A-N-Ulab/OTSI-cyberpet/graphics/otsi git baner/baner.png

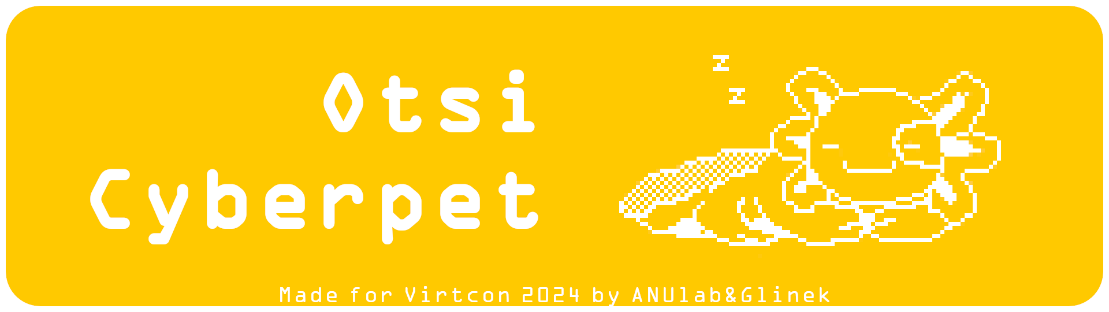
graphics/otsi git baner/baner.png
