A-N-Ulab/OTSI-cyberpet/graphics/renders and screenshots/render - back.png

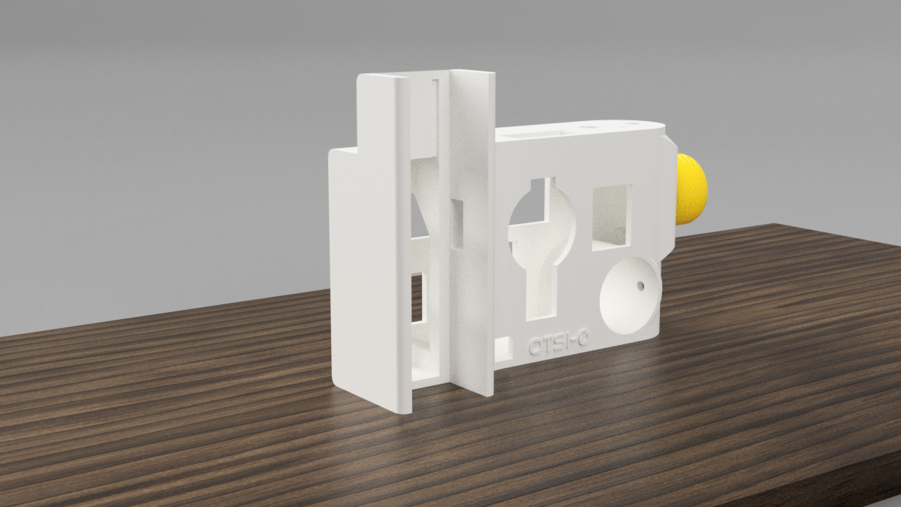
graphics/renders and screenshots/render - back.png
