A-N-Ulab/OTSI-cyberpet/graphics/renders and screenshots/render - front.png

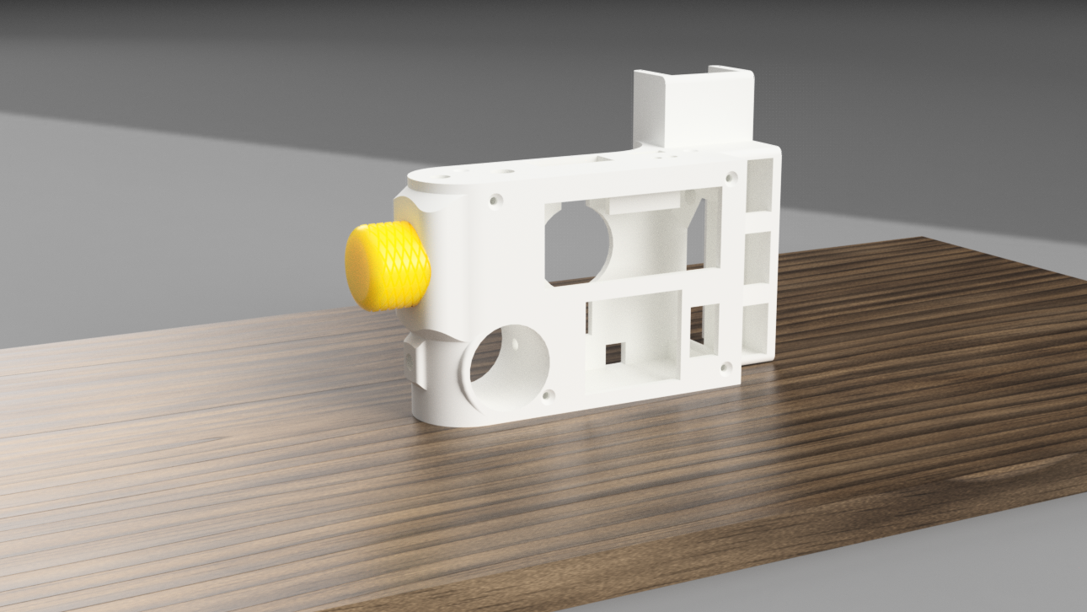
graphics/renders and screenshots/render - front.png
