A-N-Ulab/OTSI-cyberpet/graphics/renders and screenshots/render.jpg

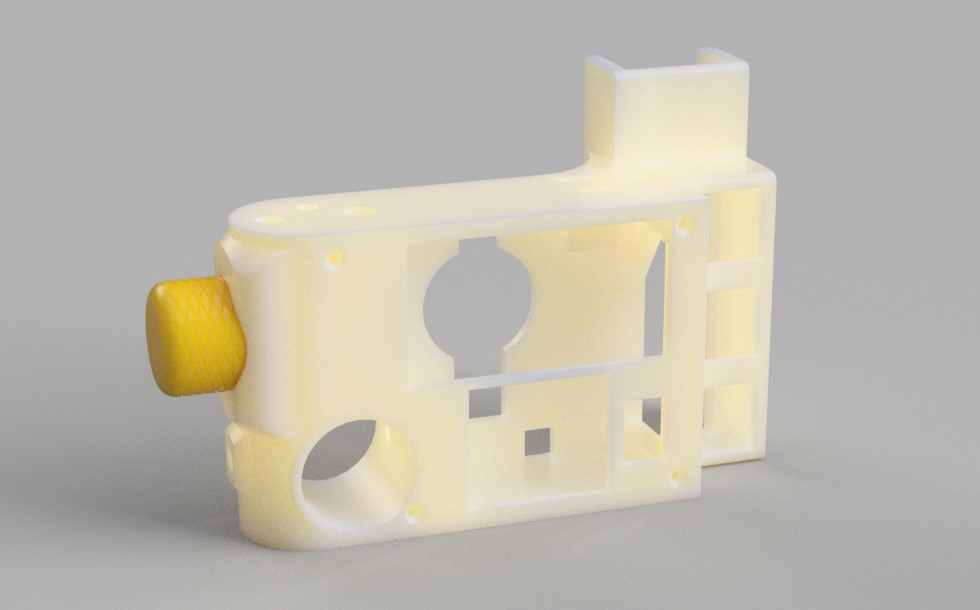
graphics/renders and screenshots/render.jpg
