A-N-Ulab/OTSI-cyberpet/graphics/renders and screenshots/Screenshot 2024-01-13 201948.jpg

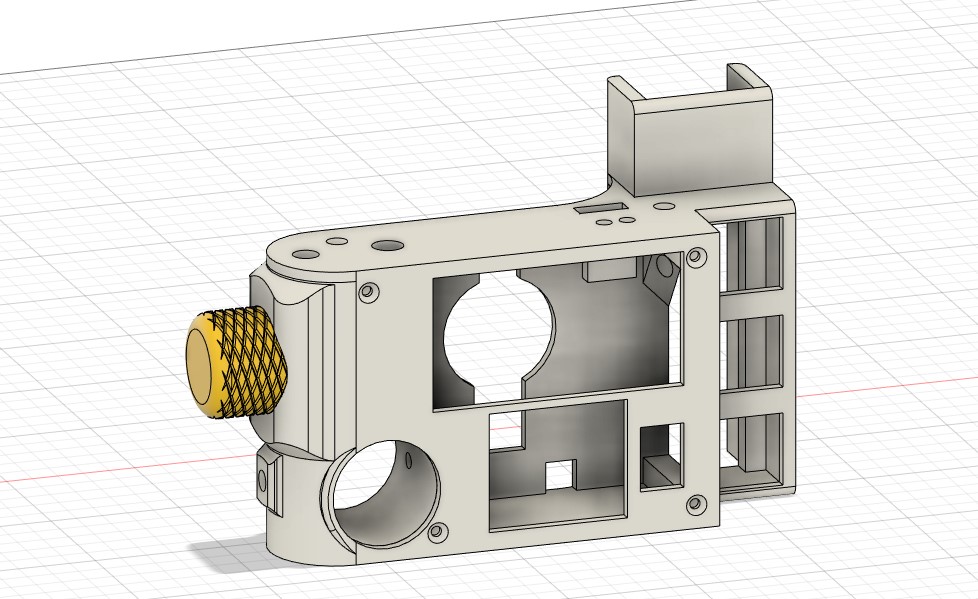
graphics/renders and screenshots/Screenshot 2024-01-13 201948.jpg
