A-N-Ulab/OTSI-cyberpet/Notes & Docs/Zrzut ekranu 2023-11-07 192916.jpg

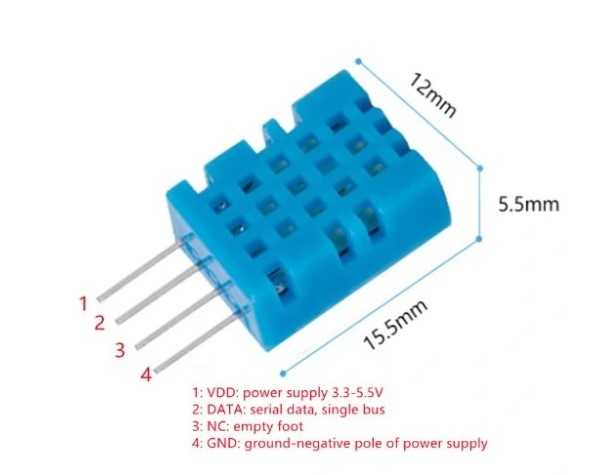
Notes & Docs/Zrzut ekranu 2023-11-07 192916.jpg
