A-N-Ulab/OTSI-cyberpet/photos/0a2272f7-c197-462a-a5be-fafe997e14a6.jpg

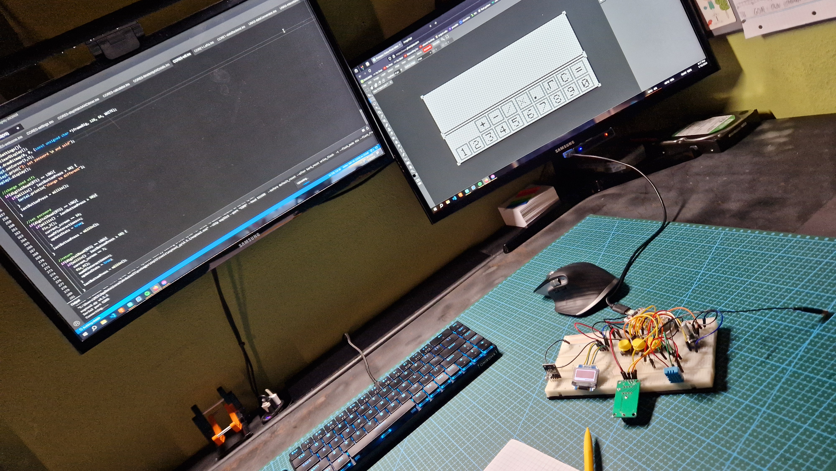
photos/0a2272f7-c197-462a-a5be-fafe997e14a6.jpg
