A-N-Ulab/OTSI-cyberpet/photos/20230913_195305.jpg

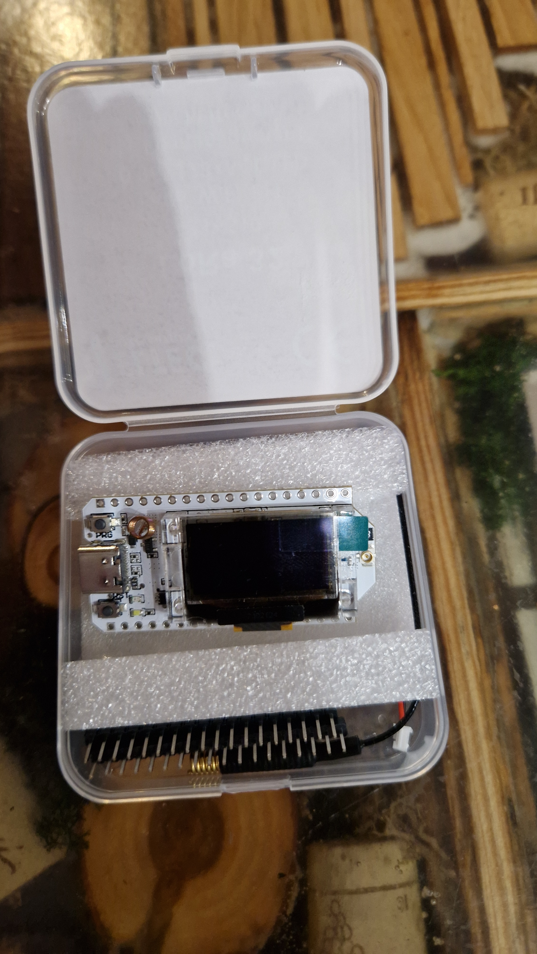
photos/20230913_195305.jpg
