A-N-Ulab/OTSI-cyberpet/photos/20230927_160514.jpg

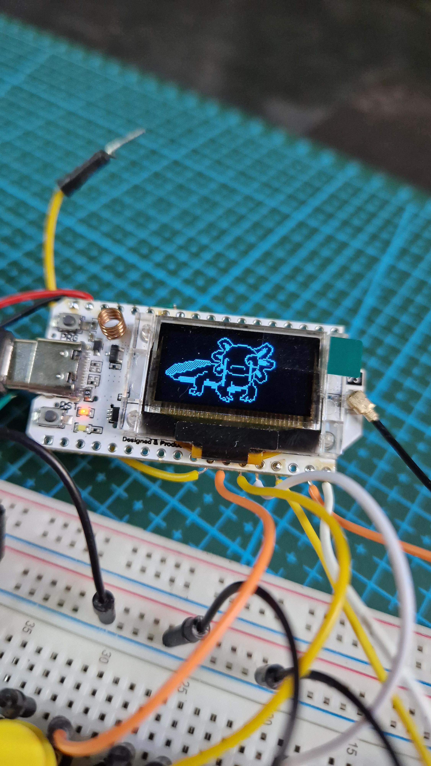
photos/20230927_160514.jpg
