A-N-Ulab/OTSI-cyberpet/photos/20230928_201221.jpg

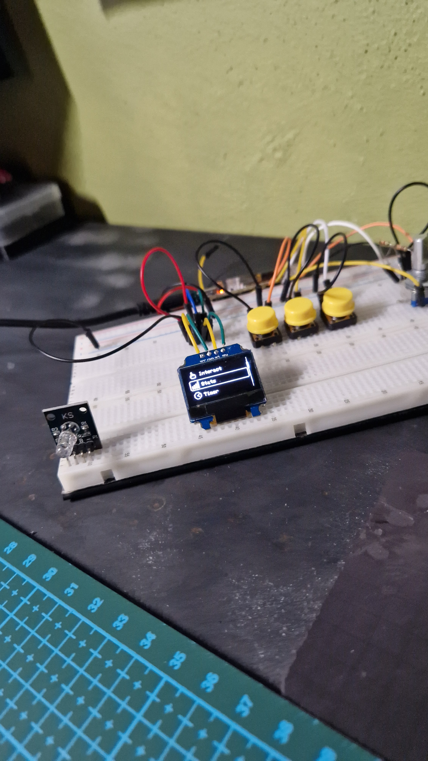
photos/20230928_201221.jpg
