A-N-Ulab/OTSI-cyberpet/photos/20231023_172651.jpg

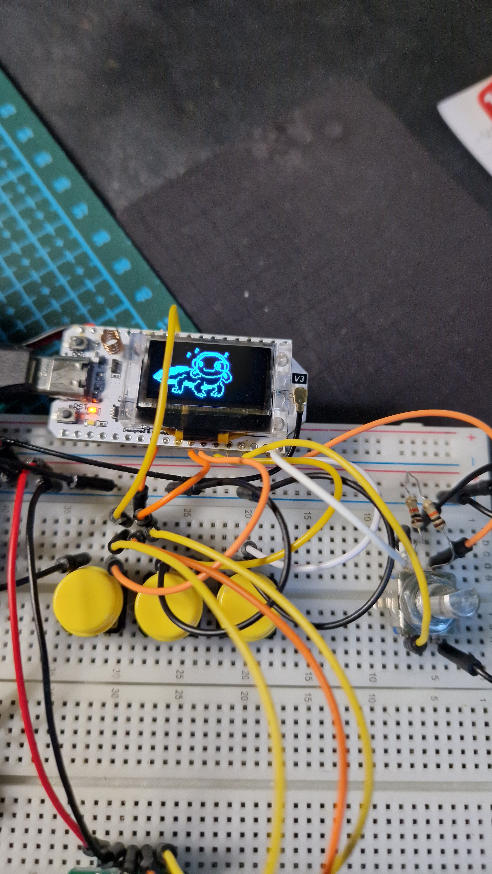
photos/20231023_172651.jpg
