A-N-Ulab/OTSI-cyberpet/photos/20240121_212100.jpg

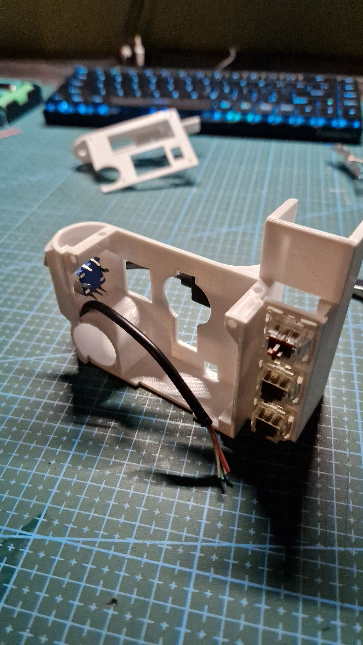
photos/20240121_212100.jpg
