A-N-Ulab/OTSI-cyberpet/photos/20240121_212102.jpg

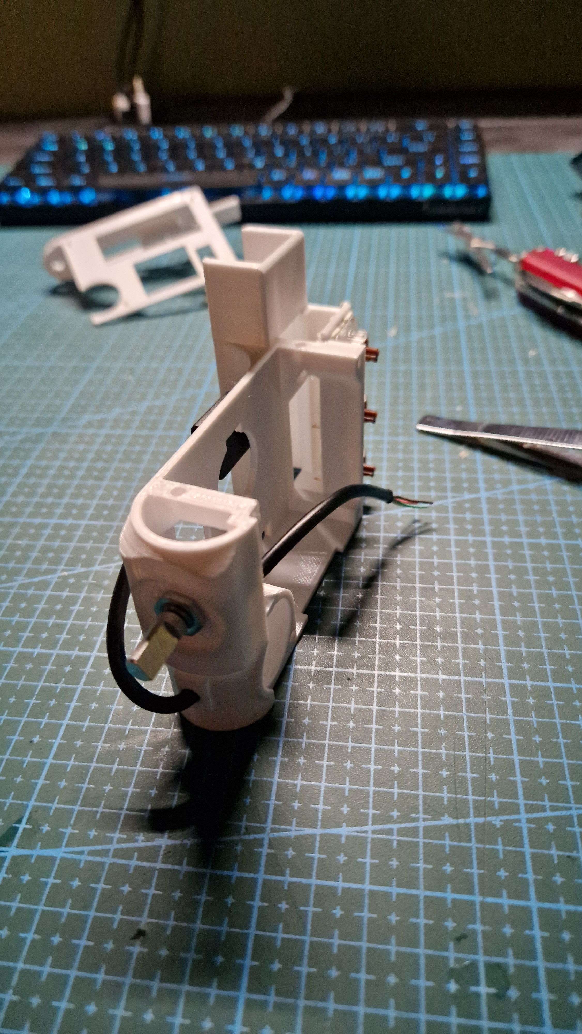
photos/20240121_212102.jpg
