A-N-Ulab/OTSI-cyberpet/photos/20240121_212109.jpg

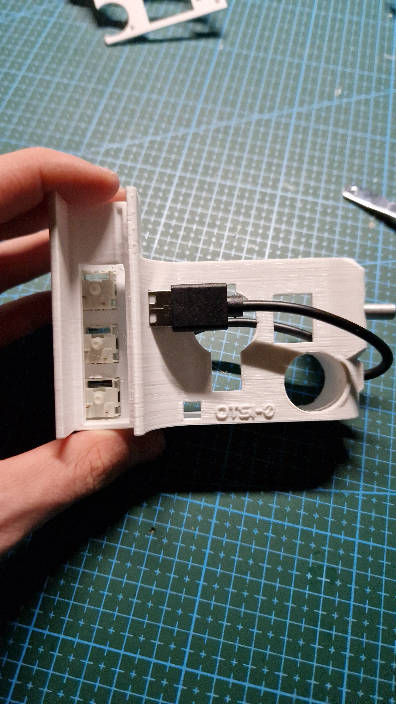
photos/20240121_212109.jpg
