A-N-Ulab/OTSI-cyberpet/photos/20240122_054914.jpg

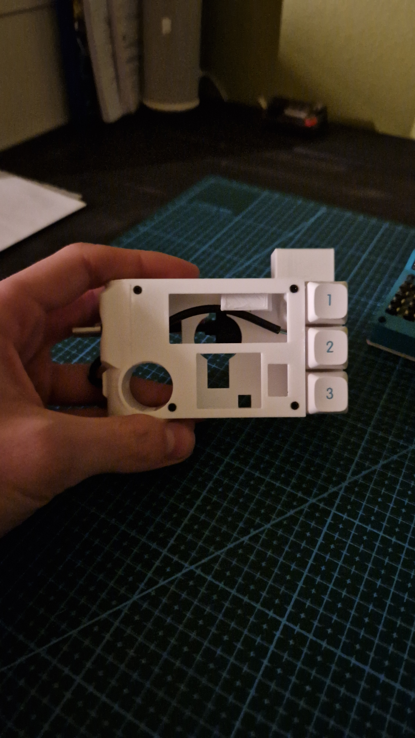
photos/20240122_054914.jpg
