A-N-Ulab/OTSI-cyberpet/photos/20240122_203220.jpg

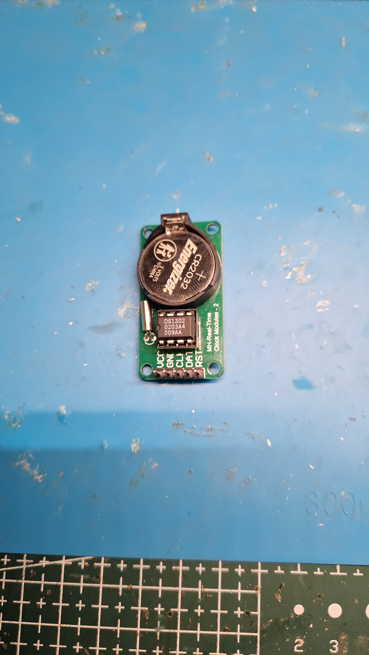
photos/20240122_203220.jpg
