A-N-Ulab/OTSI-cyberpet/photos/20240122_203737.jpg

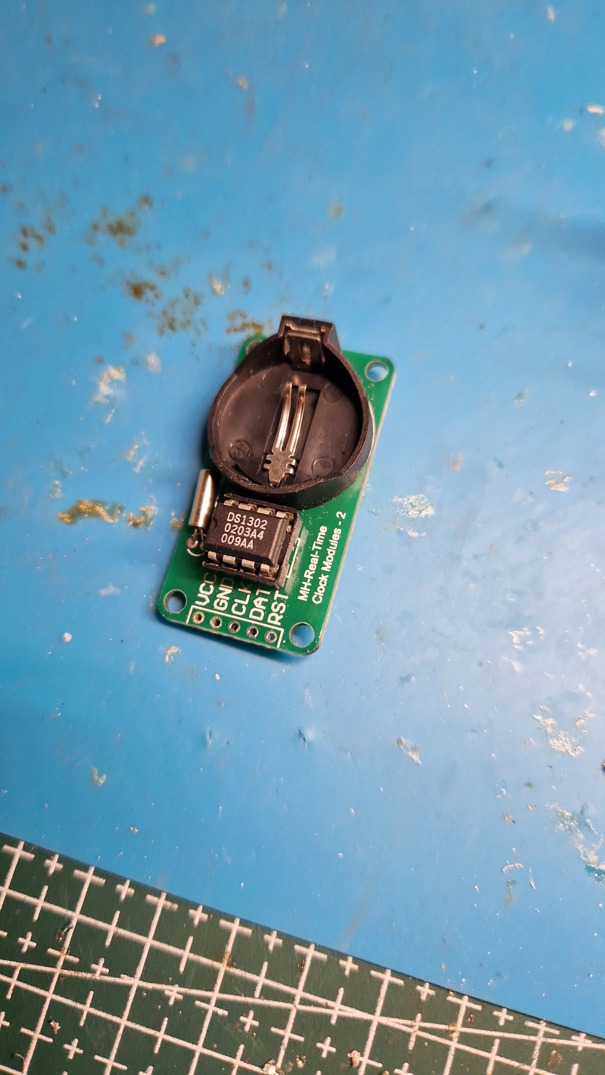
photos/20240122_203737.jpg
