A-N-Ulab/OTSI-cyberpet/photos/20240122_203856.jpg

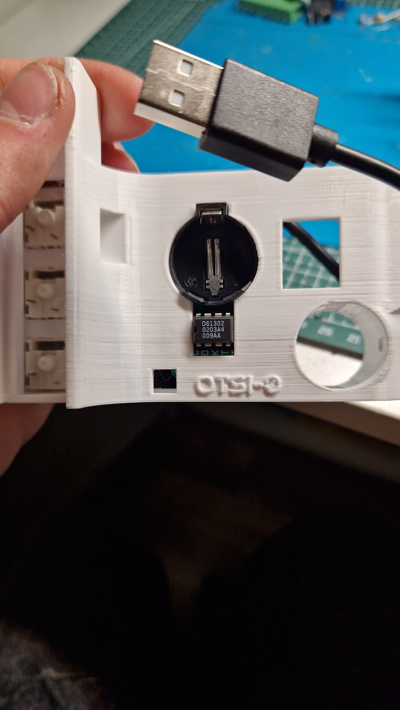
photos/20240122_203856.jpg
