A-N-Ulab/OTSI-cyberpet/photos/20240122_203859.jpg

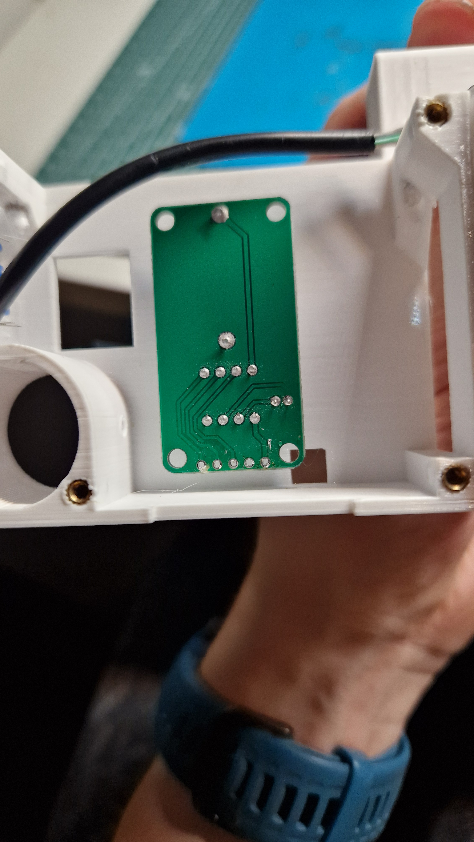
photos/20240122_203859.jpg
