A-N-Ulab/OTSI-cyberpet/photos/20240122_203900.jpg

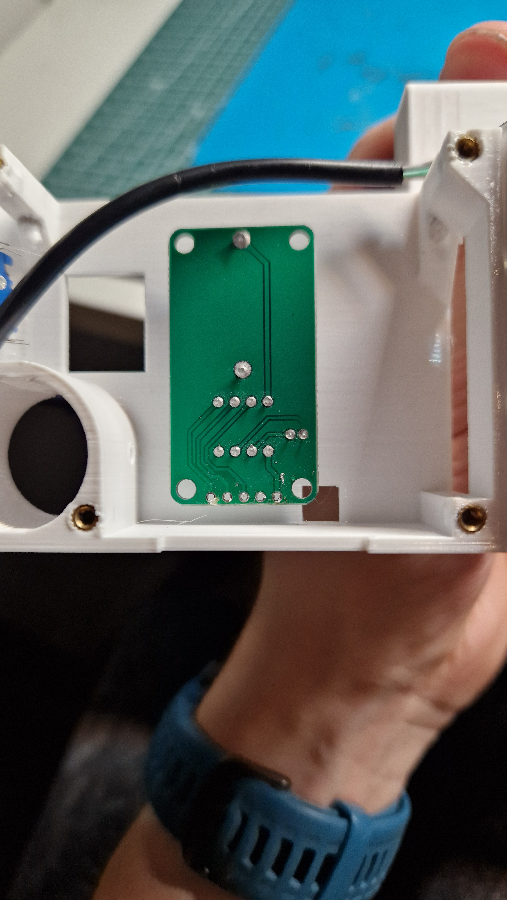
photos/20240122_203900.jpg
