A-N-Ulab/OTSI-cyberpet/photos/20240122_204321.jpg

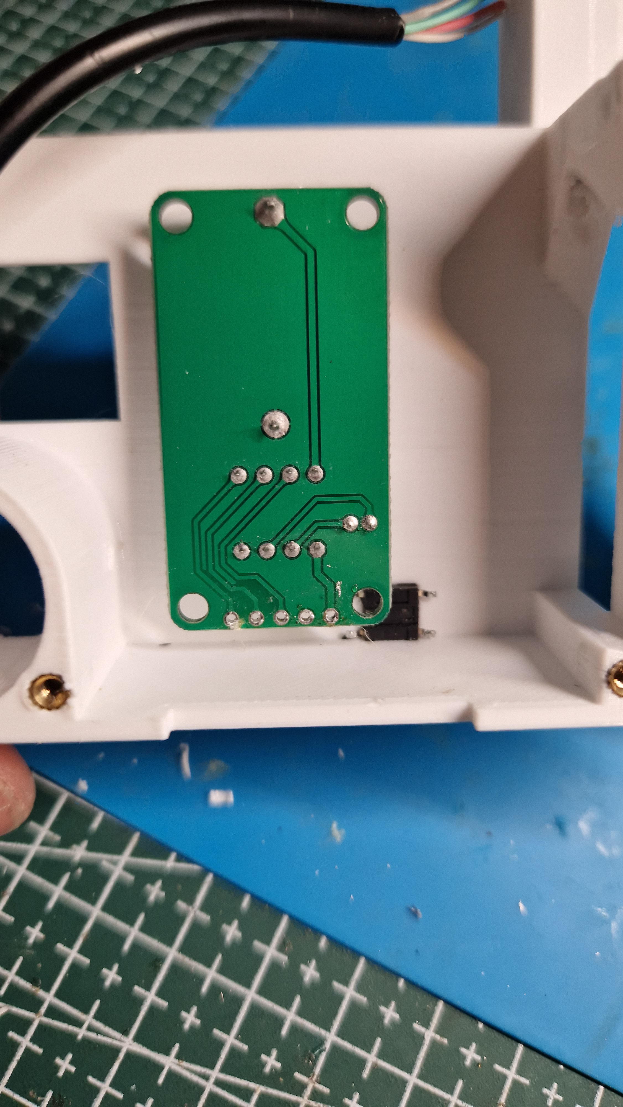
photos/20240122_204321.jpg
