A-N-Ulab/OTSI-cyberpet/photos/20240122_204324.jpg

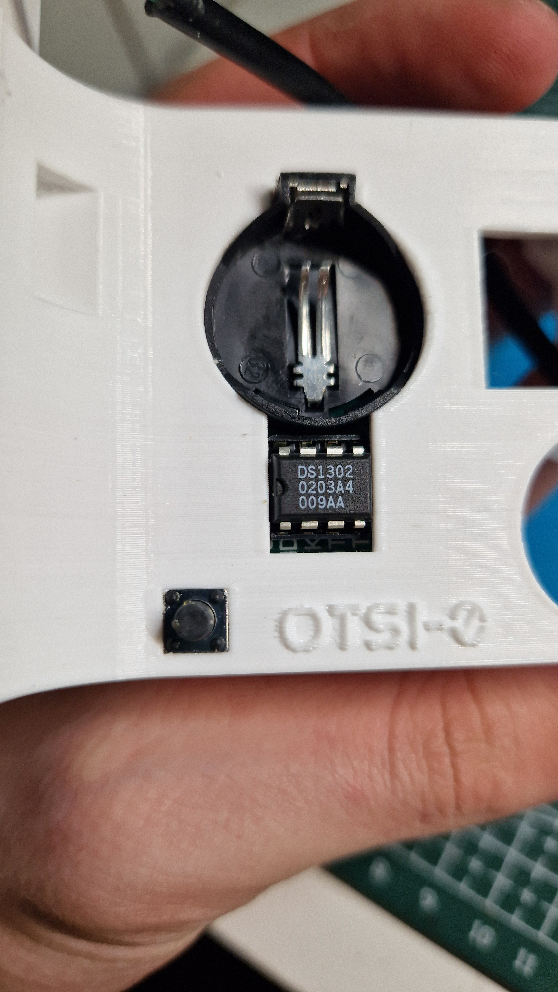
photos/20240122_204324.jpg
