A-N-Ulab/OTSI-cyberpet/photos/20240122_205355.jpg

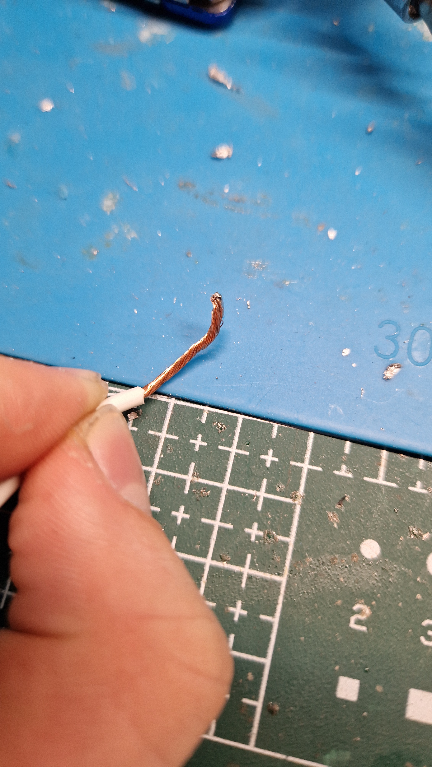
photos/20240122_205355.jpg
