A-N-Ulab/OTSI-cyberpet/photos/20240122_205412.jpg

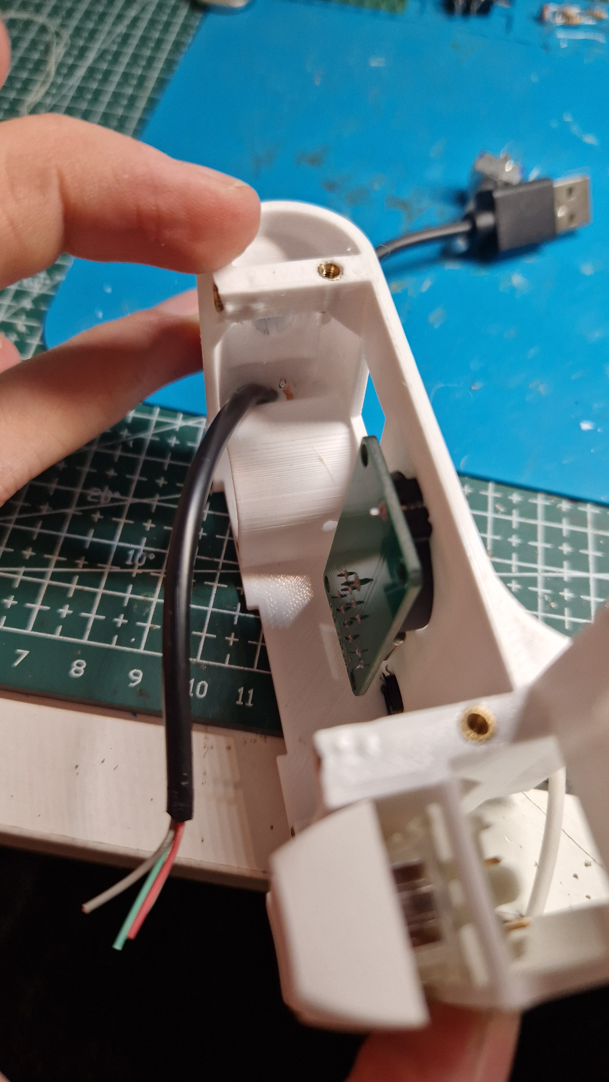
photos/20240122_205412.jpg
