A-N-Ulab/OTSI-cyberpet/photos/20240122_205949.jpg

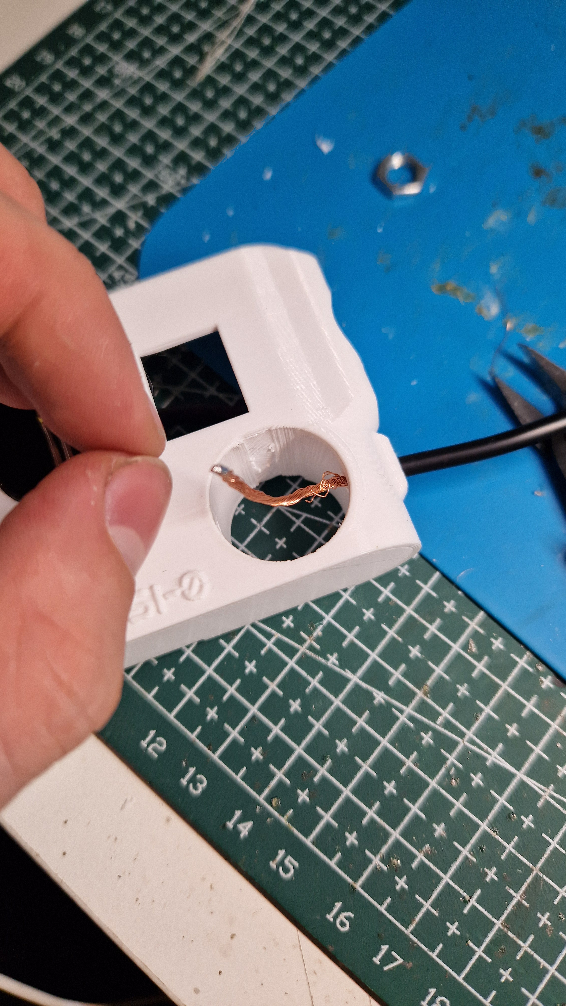
photos/20240122_205949.jpg
