A-N-Ulab/OTSI-cyberpet/photos/20240122_205954.jpg

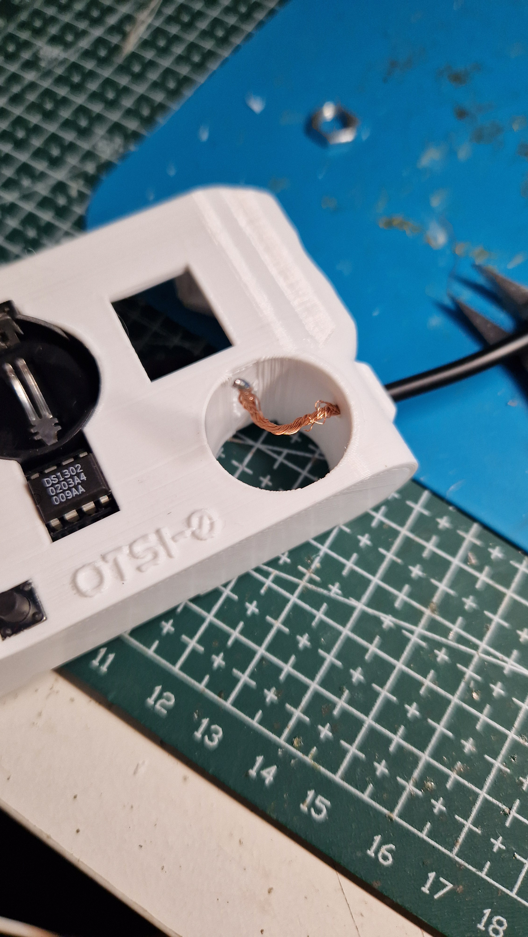
photos/20240122_205954.jpg
