A-N-Ulab/OTSI-cyberpet/photos/20240122_210243.jpg

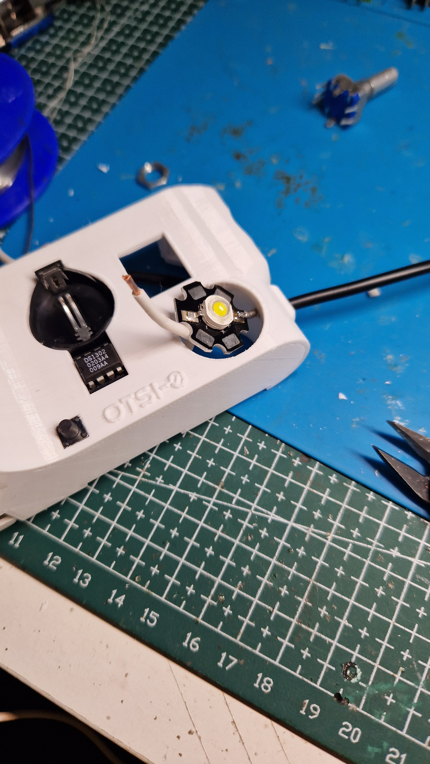
photos/20240122_210243.jpg
