A-N-Ulab/OTSI-cyberpet/photos/20240122_210559.jpg

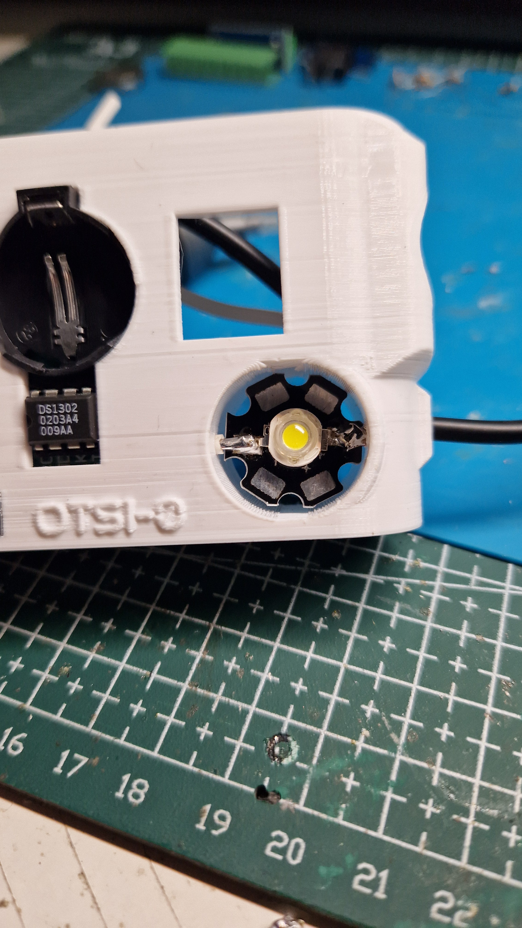
photos/20240122_210559.jpg
