A-N-Ulab/OTSI-cyberpet/photos/20240122_210723.jpg

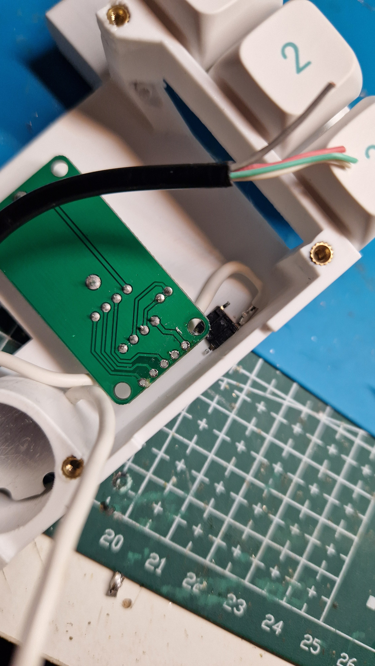
photos/20240122_210723.jpg
