A-N-Ulab/OTSI-cyberpet/photos/20240122_210949.jpg

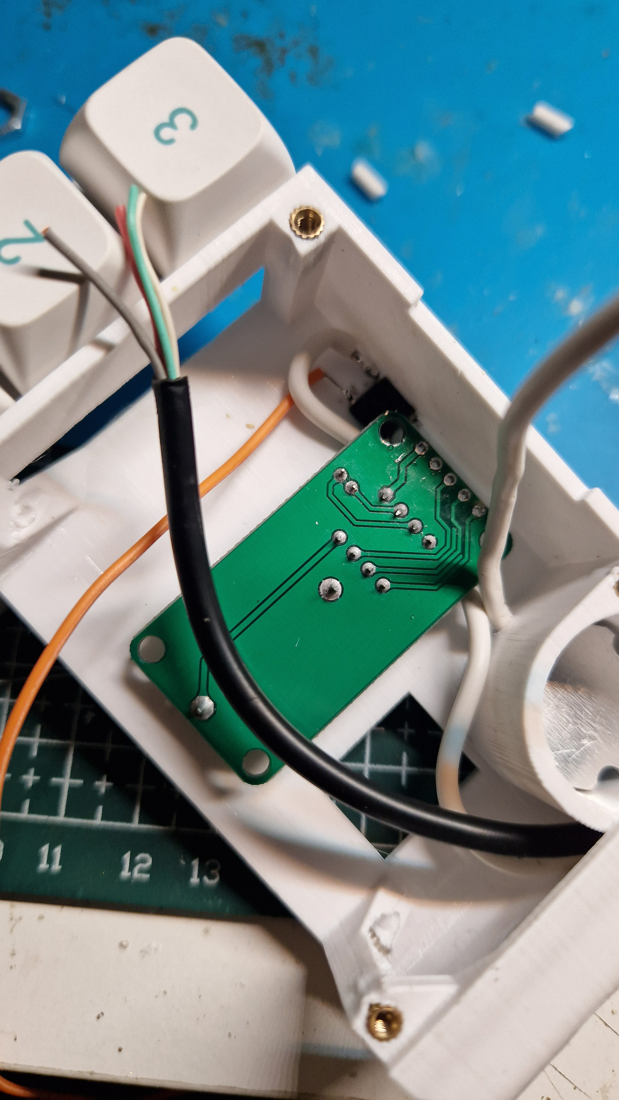
photos/20240122_210949.jpg
