A-N-Ulab/OTSI-cyberpet/photos/20240122_211322.jpg

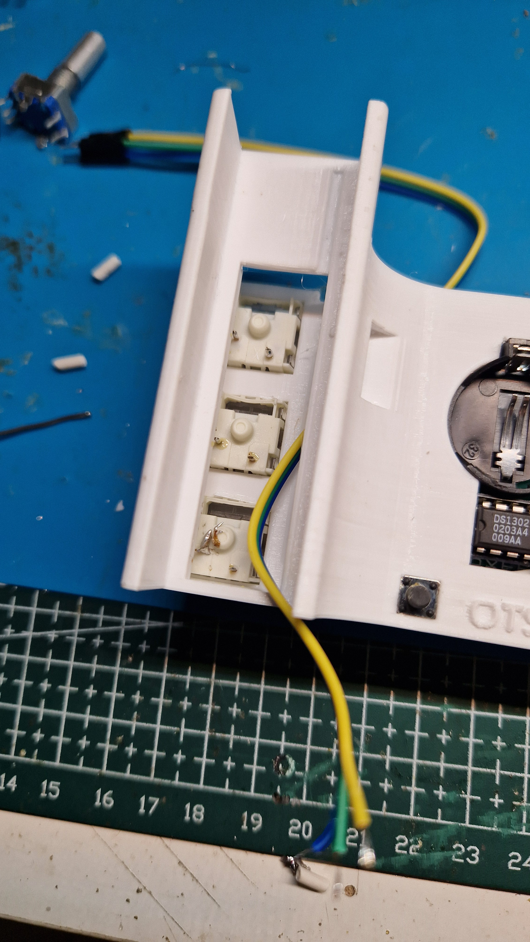
photos/20240122_211322.jpg
