A-N-Ulab/OTSI-cyberpet/photos/20240122_211459.jpg

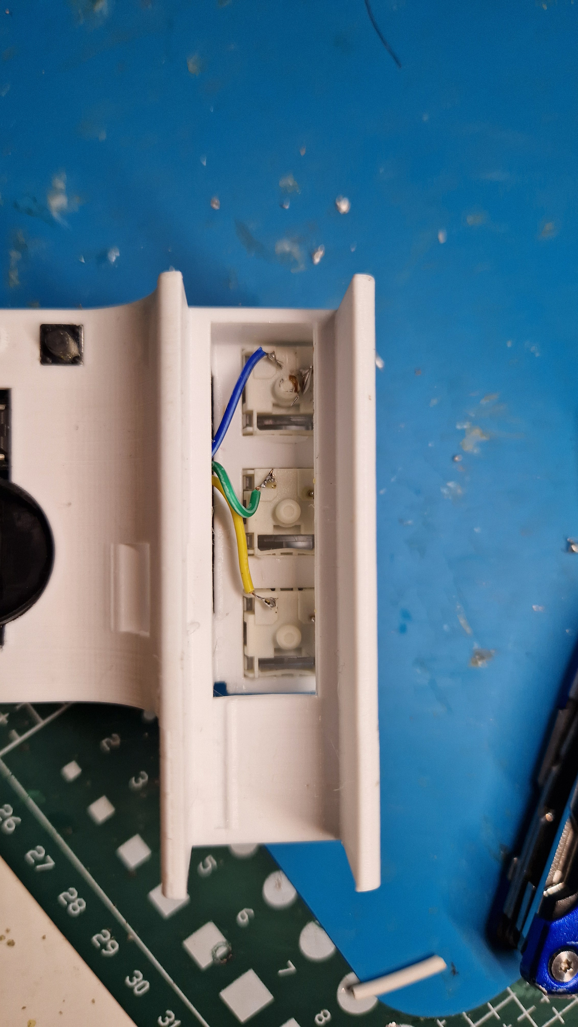
photos/20240122_211459.jpg
