A-N-Ulab/OTSI-cyberpet/photos/20240122_211742.jpg

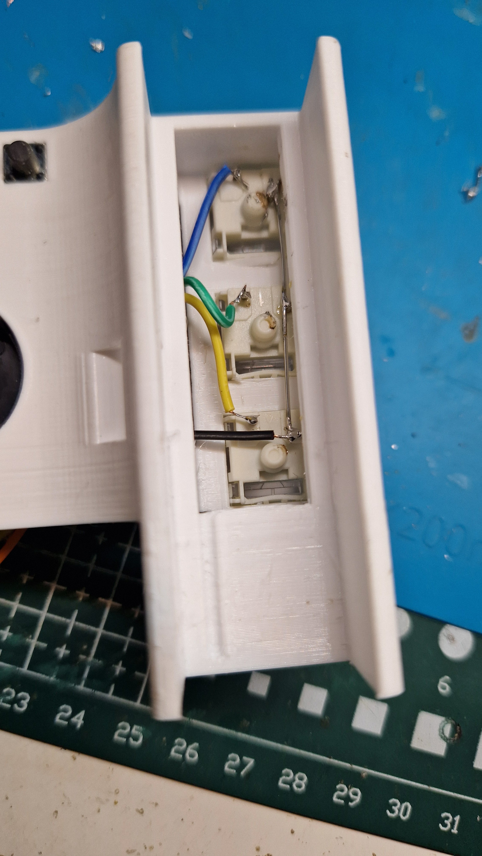
photos/20240122_211742.jpg
