A-N-Ulab/OTSI-cyberpet/photos/20240122_211933.jpg

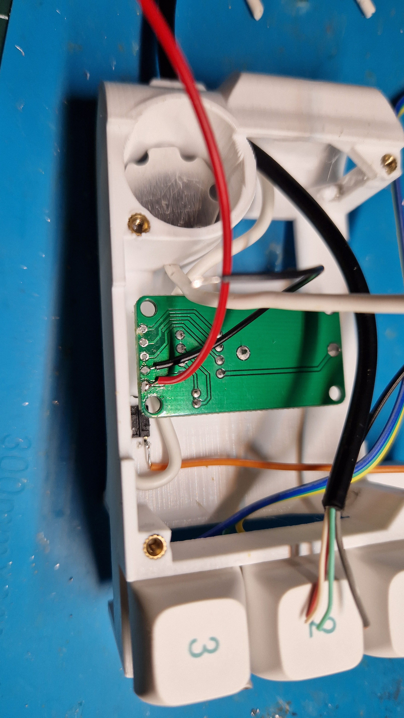
photos/20240122_211933.jpg
