A-N-Ulab/OTSI-cyberpet/photos/20240122_212038.jpg

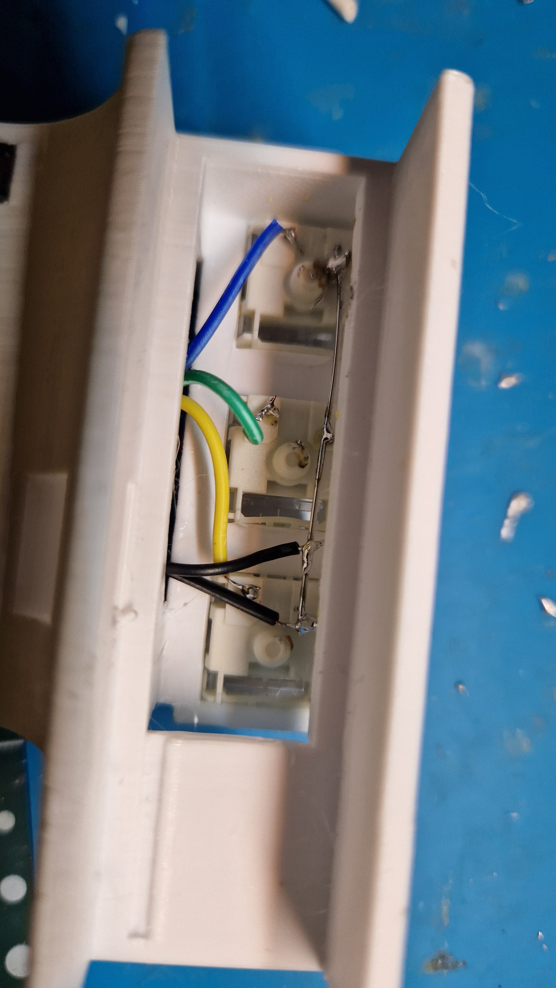
photos/20240122_212038.jpg
