A-N-Ulab/OTSI-cyberpet/photos/20240122_212201.jpg

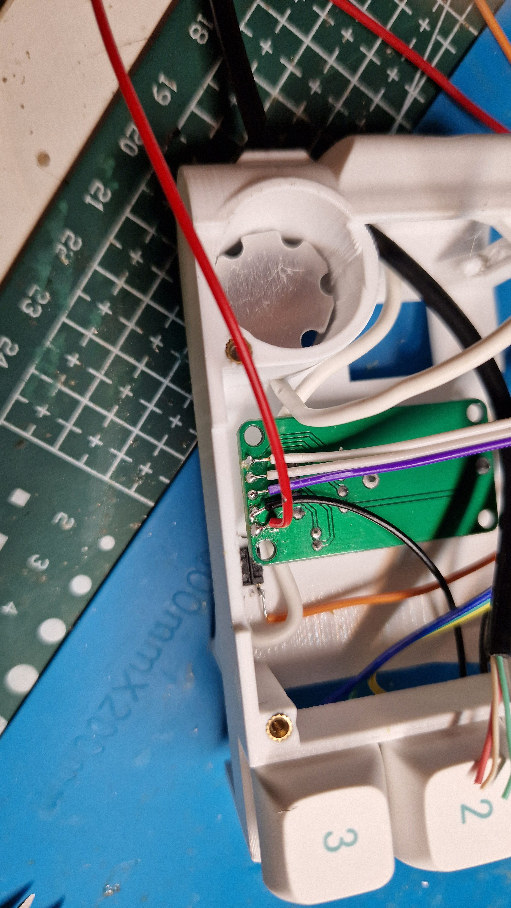
photos/20240122_212201.jpg
