A-N-Ulab/OTSI-cyberpet/photos/20240122_212416.jpg

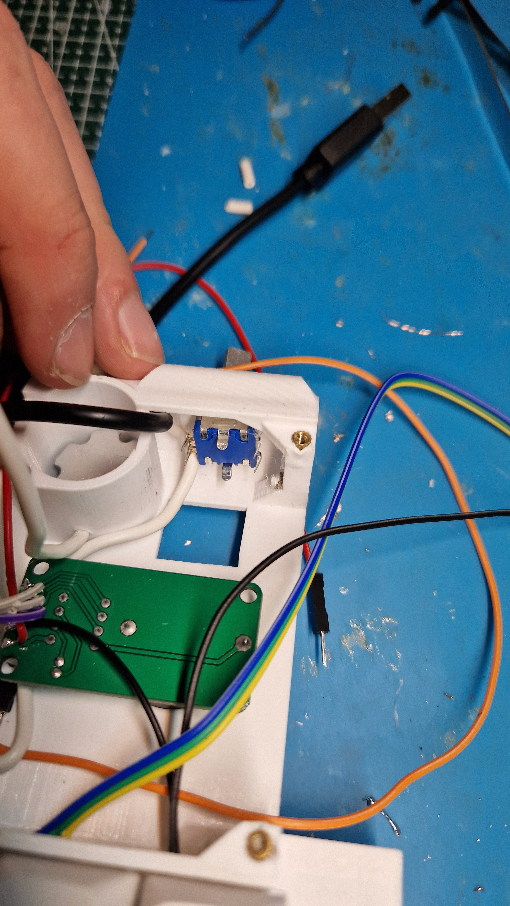
photos/20240122_212416.jpg
