A-N-Ulab/OTSI-cyberpet/photos/20240122_213624.jpg

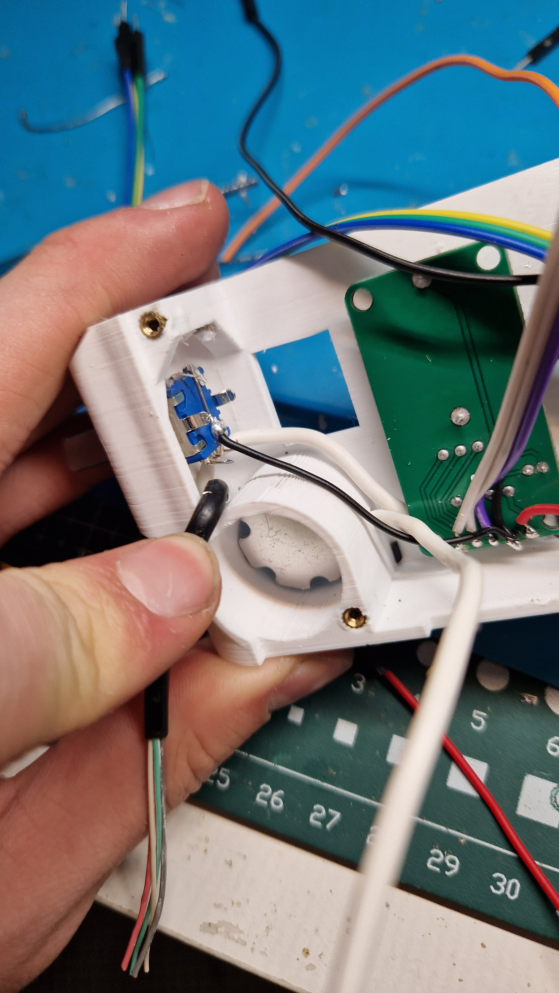
photos/20240122_213624.jpg
