A-N-Ulab/OTSI-cyberpet/photos/20240122_213839.jpg

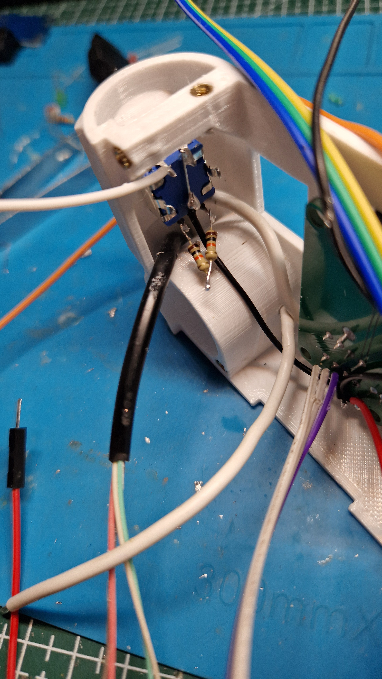
photos/20240122_213839.jpg
