A-N-Ulab/OTSI-cyberpet/photos/20240122_214125.jpg

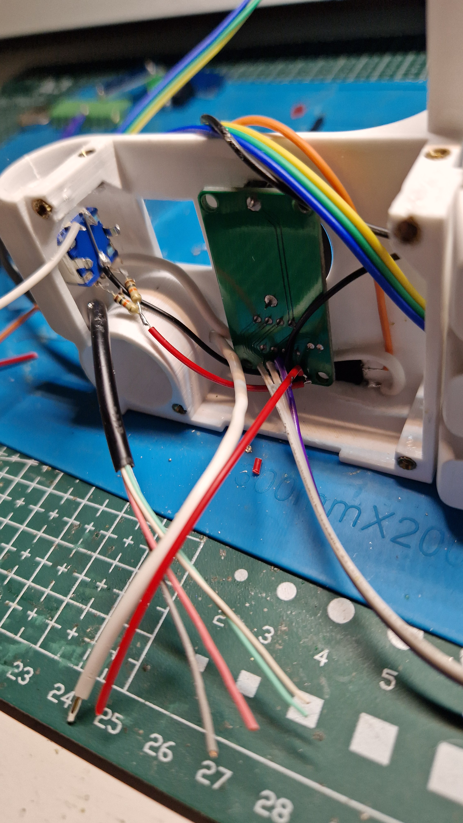
photos/20240122_214125.jpg
