A-N-Ulab/OTSI-cyberpet/photos/20240122_214958.jpg

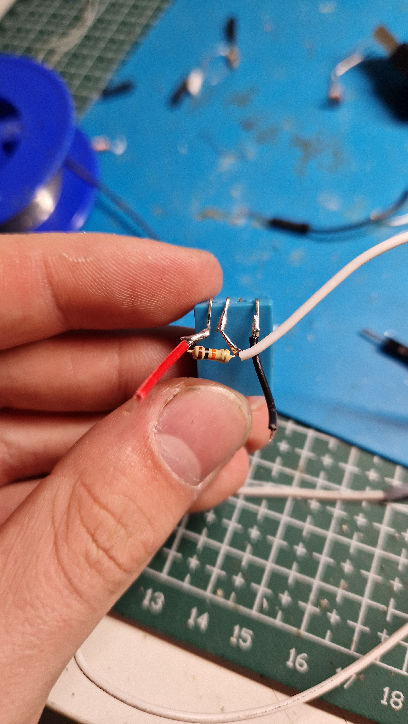
photos/20240122_214958.jpg
