A-N-Ulab/OTSI-cyberpet/photos/20240122_220841.jpg

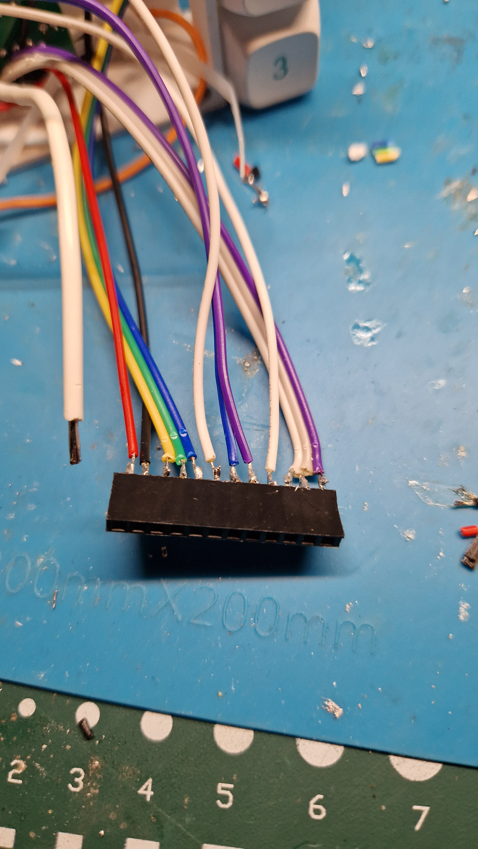
photos/20240122_220841.jpg
