A-N-Ulab/OTSI-cyberpet/photos/20240122_221745.jpg

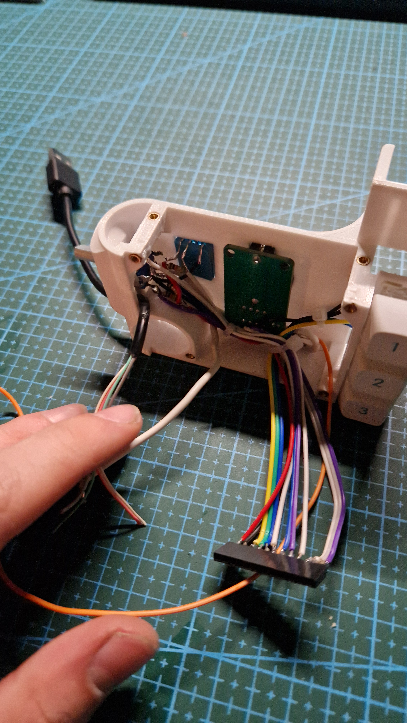
photos/20240122_221745.jpg
