A-N-Ulab/OTSI-cyberpet/photos/20240123_164509.jpg

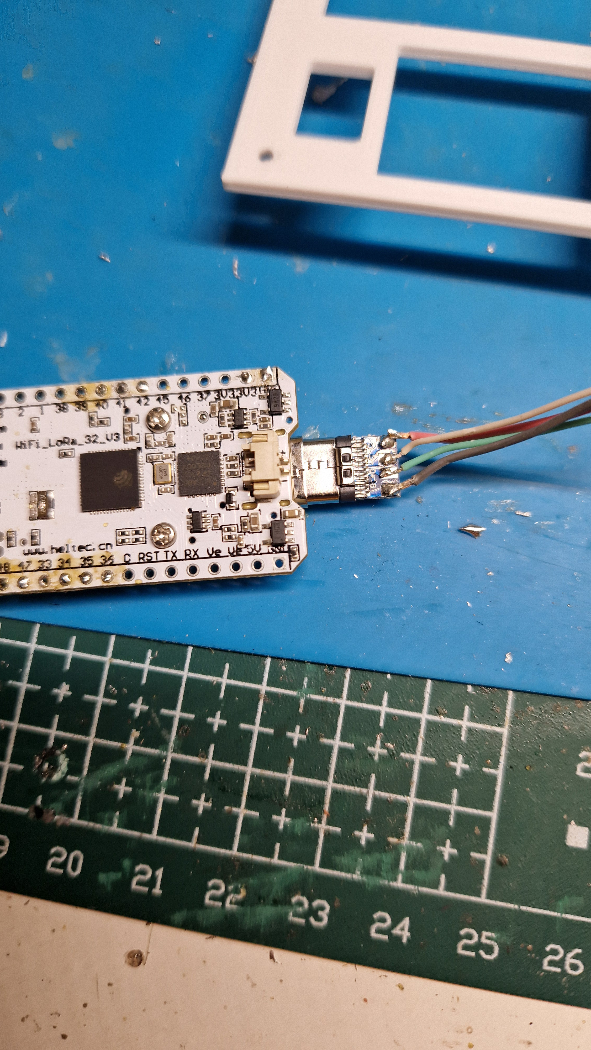
photos/20240123_164509.jpg
