A-N-Ulab/OTSI-cyberpet/photos/20240123_164611.jpg

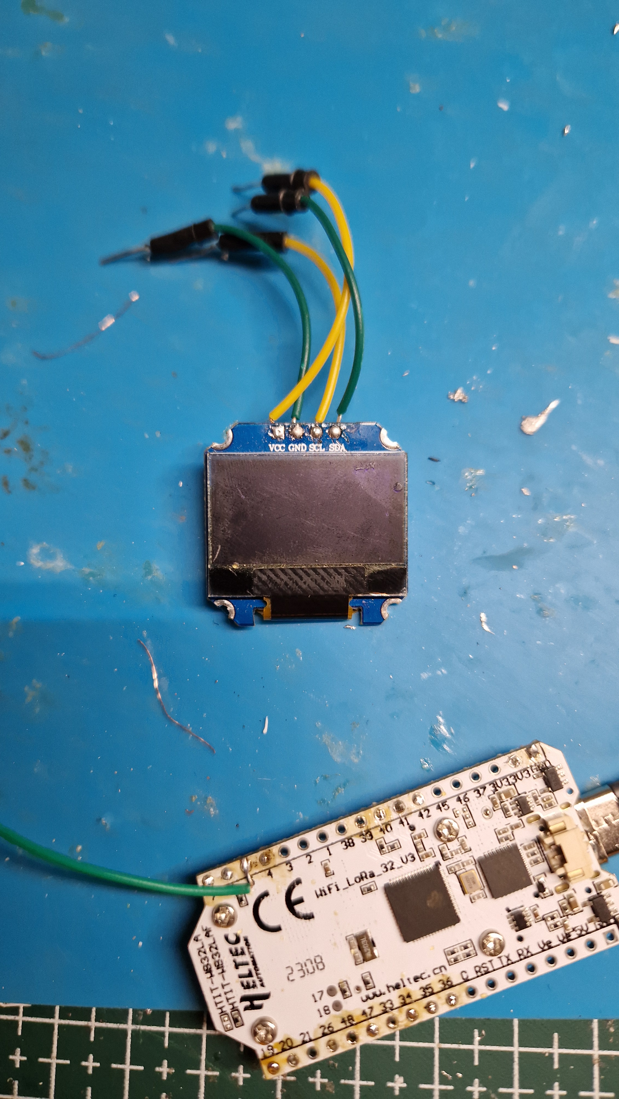
photos/20240123_164611.jpg
