A-N-Ulab/OTSI-cyberpet/photos/20240123_165450.jpg

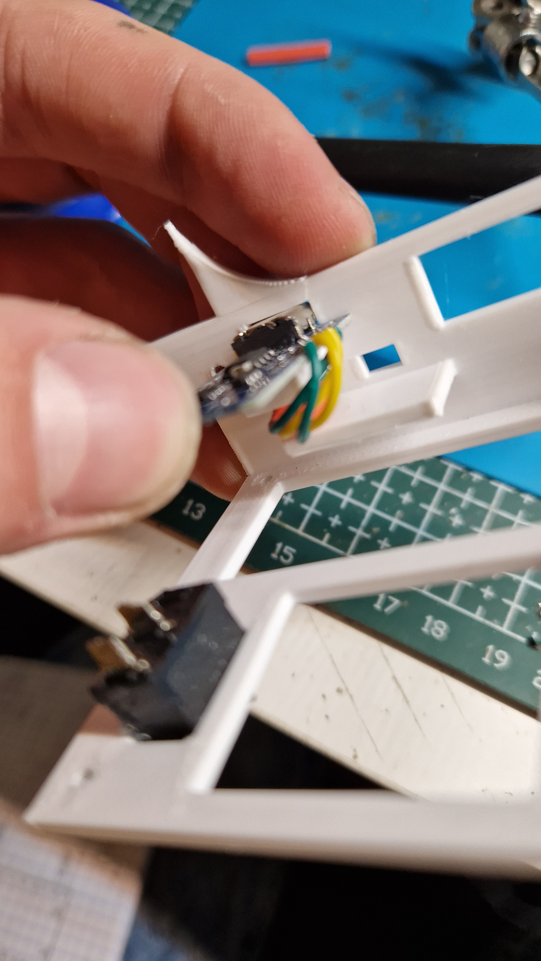
photos/20240123_165450.jpg
