A-N-Ulab/OTSI-cyberpet/photos/20240123_172744.jpg

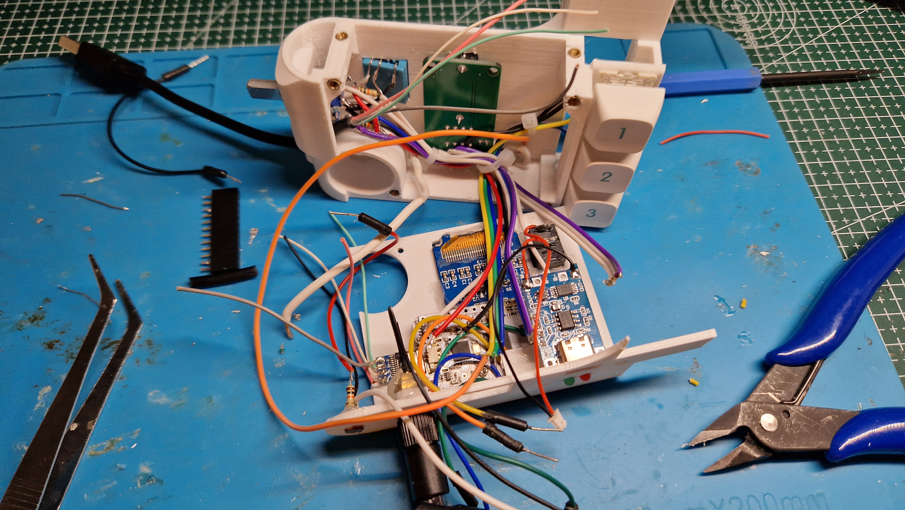
photos/20240123_172744.jpg
