A-N-Ulab/OTSI-cyberpet/photos/20240123_211852.jpg

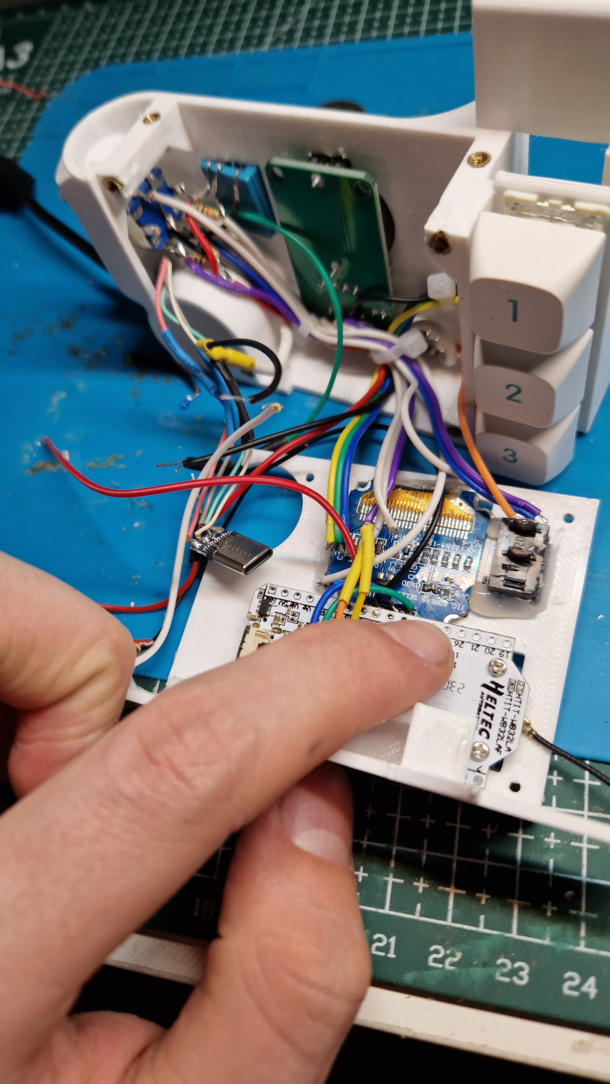
photos/20240123_211852.jpg
