A-N-Ulab/OTSI-cyberpet/photos/20240123_223442.jpg

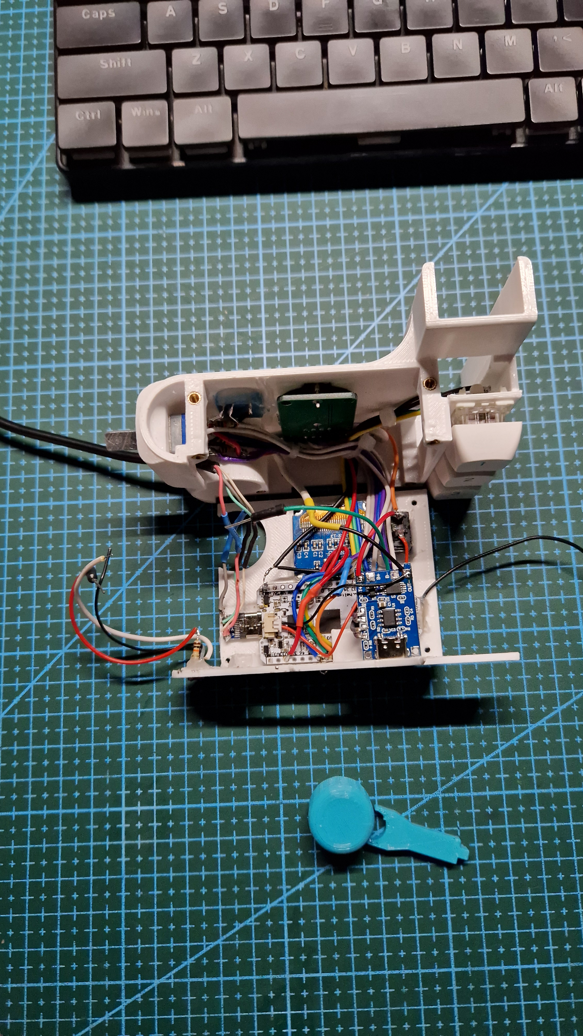
photos/20240123_223442.jpg
