A-N-Ulab/OTSI-cyberpet/photos/20240124_095504.jpg

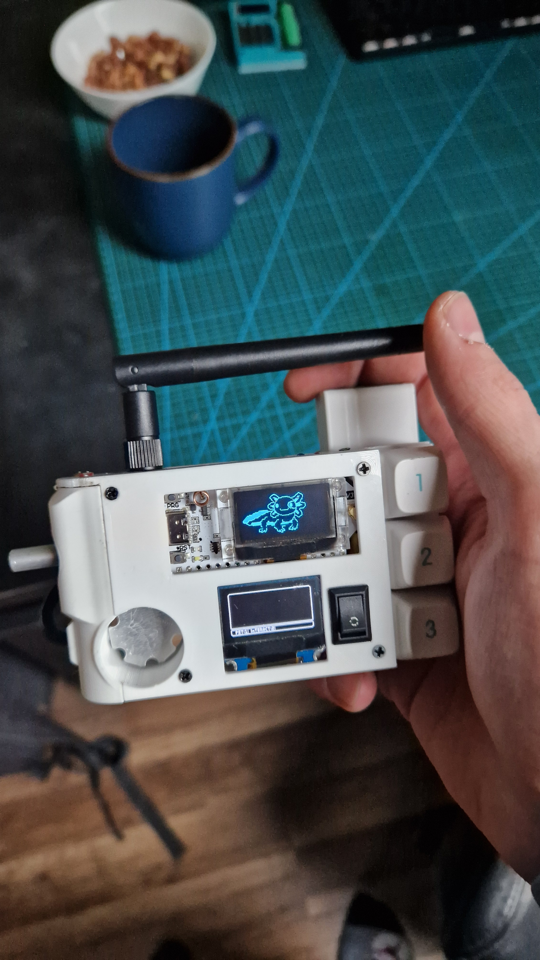
photos/20240124_095504.jpg
