A-N-Ulab/OTSI-cyberpet/photos/20240124_214952.jpg

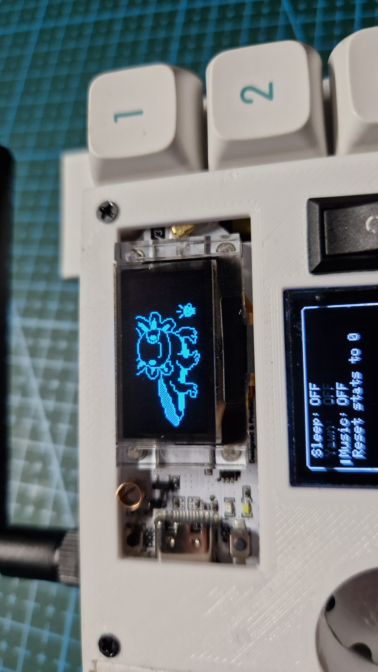
photos/20240124_214952.jpg
