A-N-Ulab/OTSI-cyberpet/photos/20240127_142506.jpg

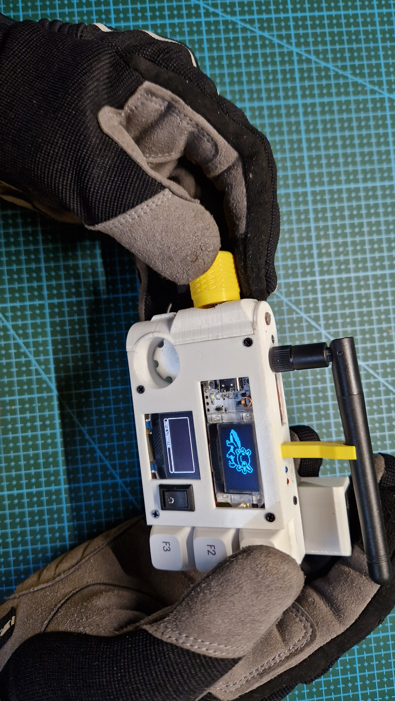
photos/20240127_142506.jpg
