A-N-Ulab/OTSI-cyberpet/photos/20240127_143146.jpg

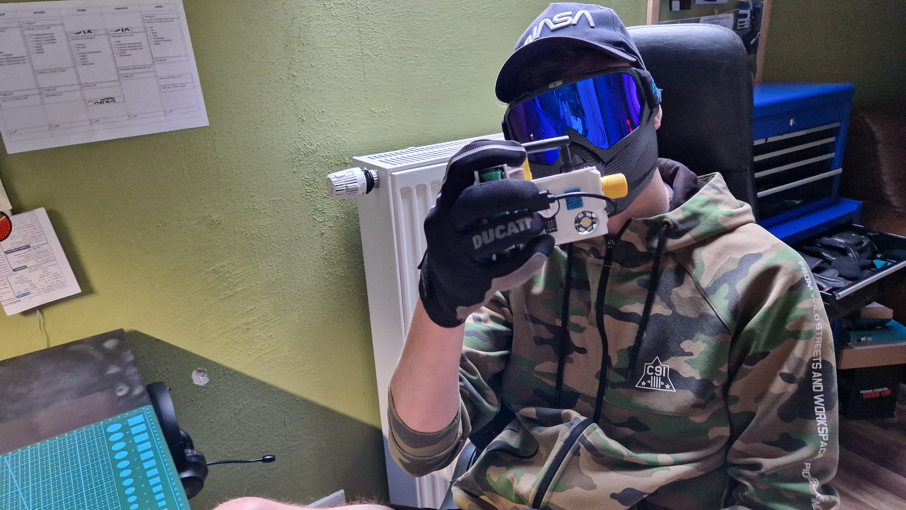
photos/20240127_143146.jpg
