A-N-Ulab/OTSI-cyberpet/photos/20240127_143203.jpg

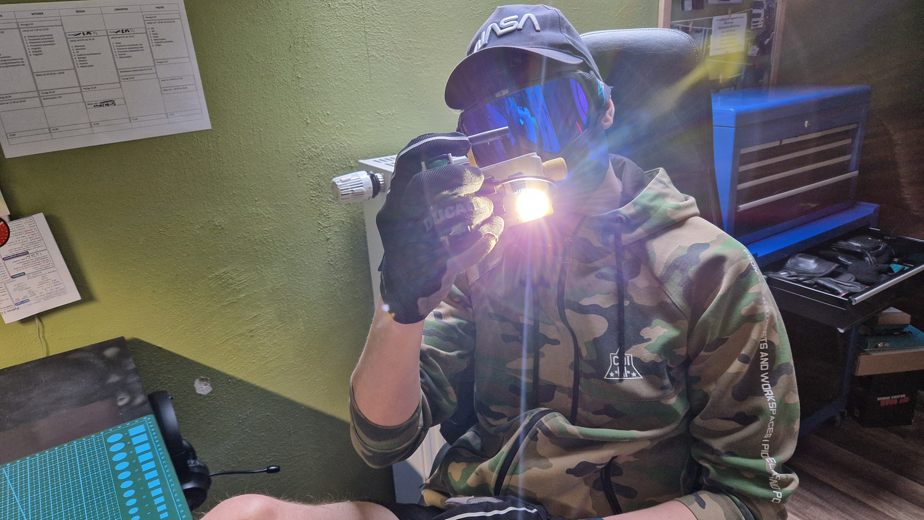
photos/20240127_143203.jpg
