A-N-Ulab/OTSI-cyberpet/photos/20240127_143508.jpg

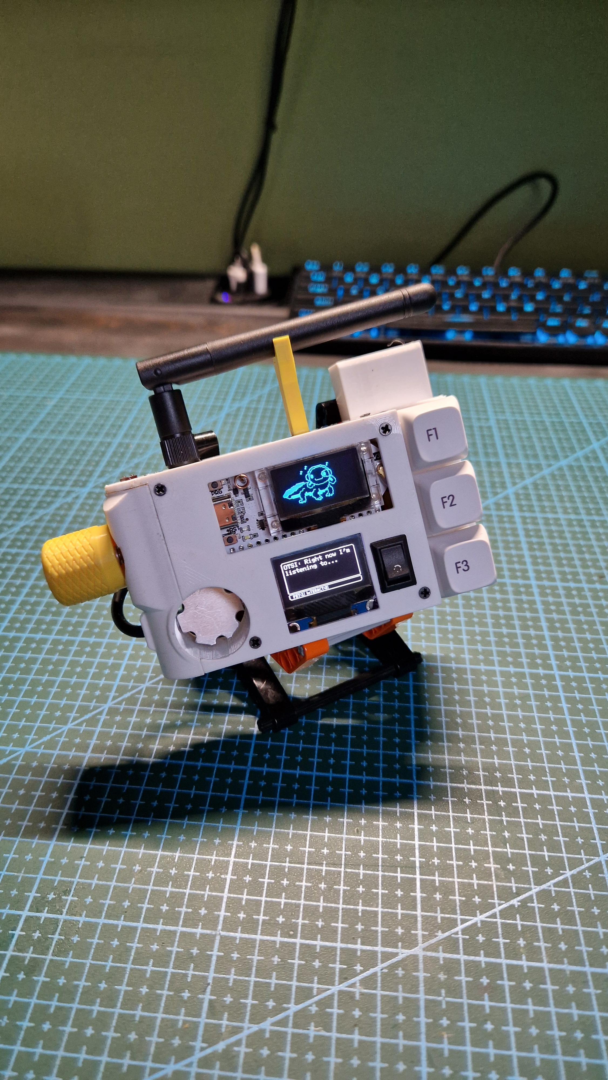
photos/20240127_143508.jpg
