A-N-Ulab/OTSI-cyberpet/photos/20240127_143510.jpg

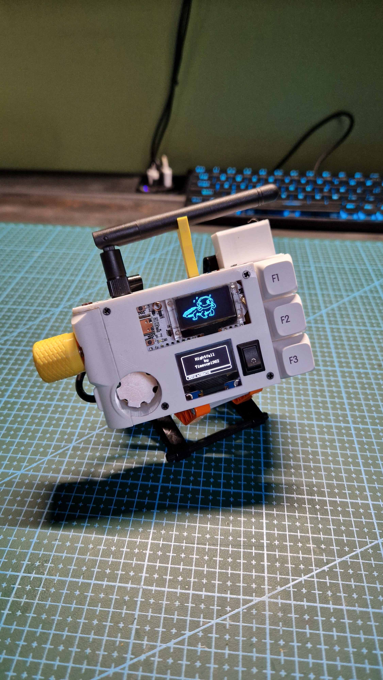
photos/20240127_143510.jpg
