A-N-Ulab/OTSI-cyberpet/photos/20240127_143534.jpg

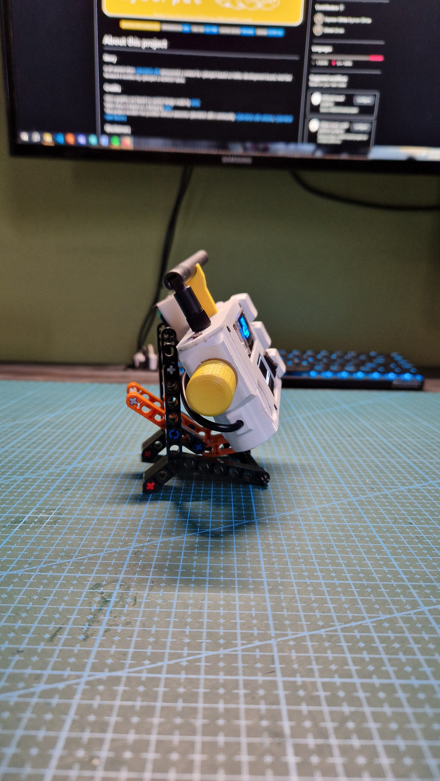
photos/20240127_143534.jpg
