A-N-Ulab/OTSI-cyberpet/photos/20240127_143543.jpg

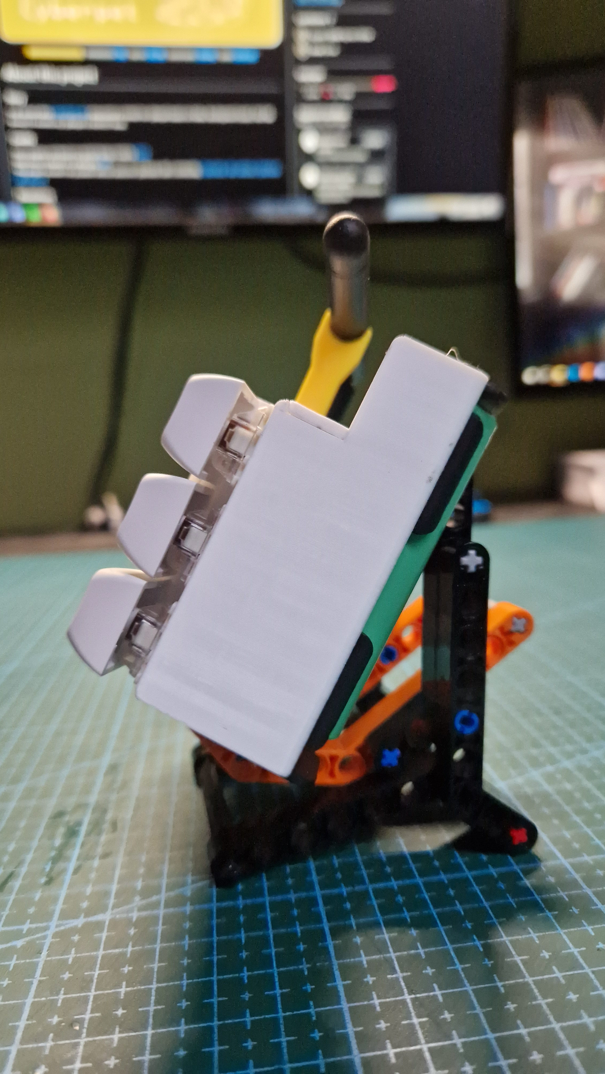
photos/20240127_143543.jpg
