A-N-Ulab/OTSI-cyberpet/photos/20240127_143608.jpg

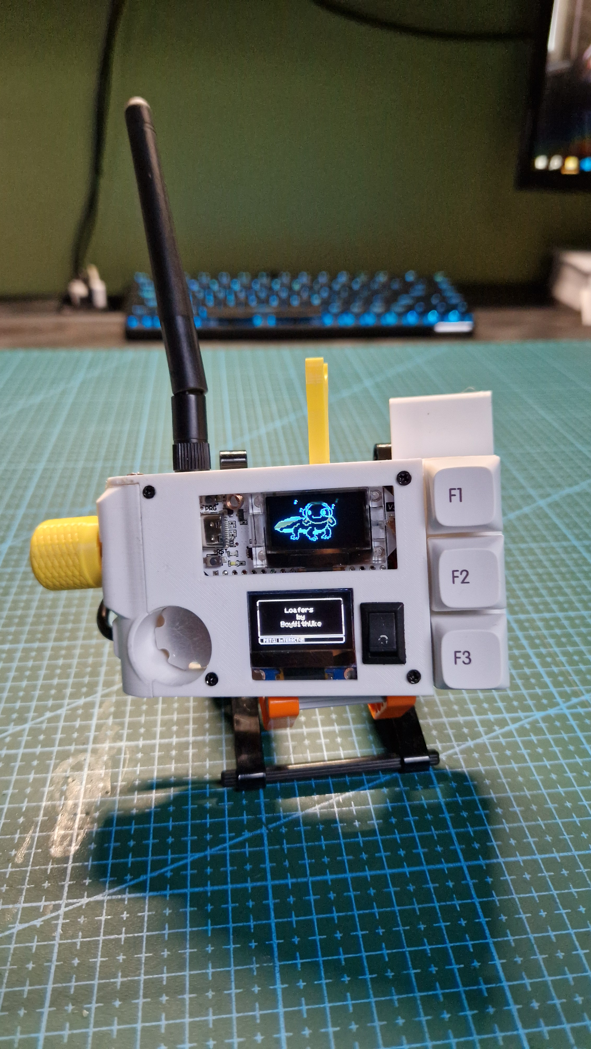
photos/20240127_143608.jpg
