A-N-Ulab/OTSI-cyberpet/photos/20240127_143644.jpg

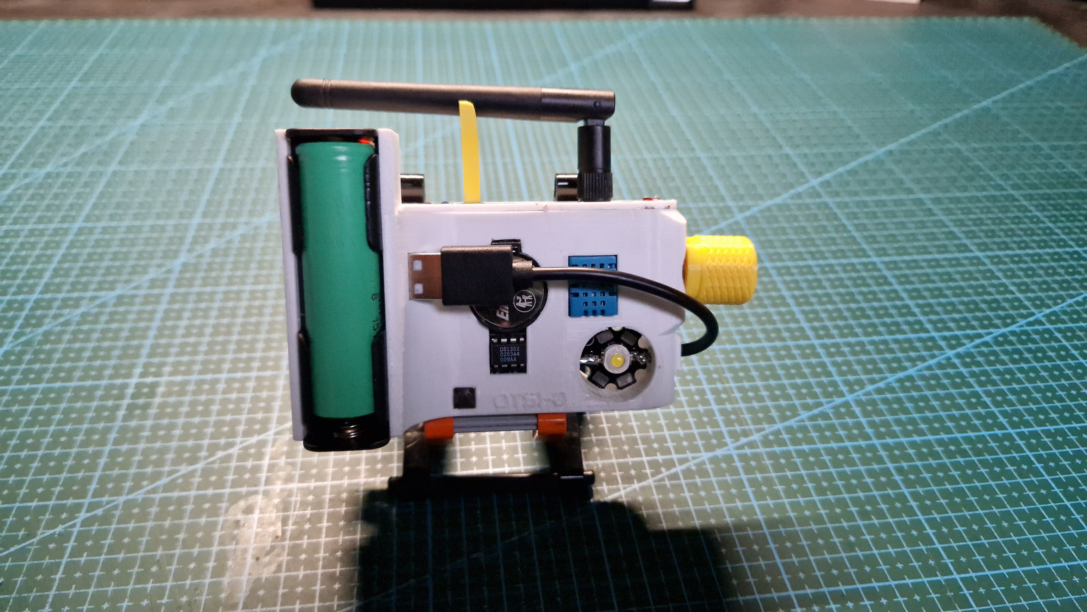
photos/20240127_143644.jpg
