A-N-Ulab/OTSI-cyberpet/photos/20240127_143650.jpg

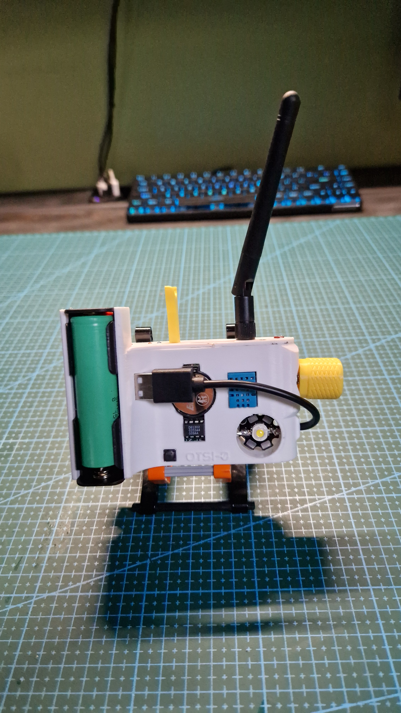
photos/20240127_143650.jpg
