A-N-Ulab/OTSI-cyberpet/photos/20240127_143704.jpg

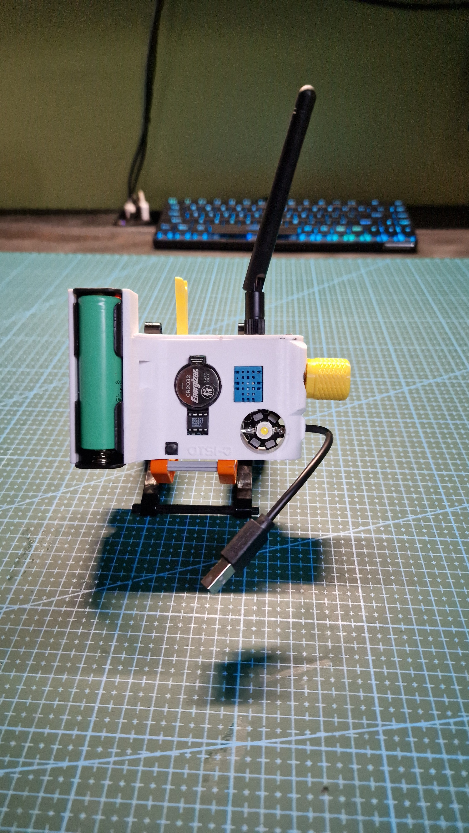
photos/20240127_143704.jpg
