A-N-Ulab/OTSI-cyberpet/photos/20240127_143712.jpg

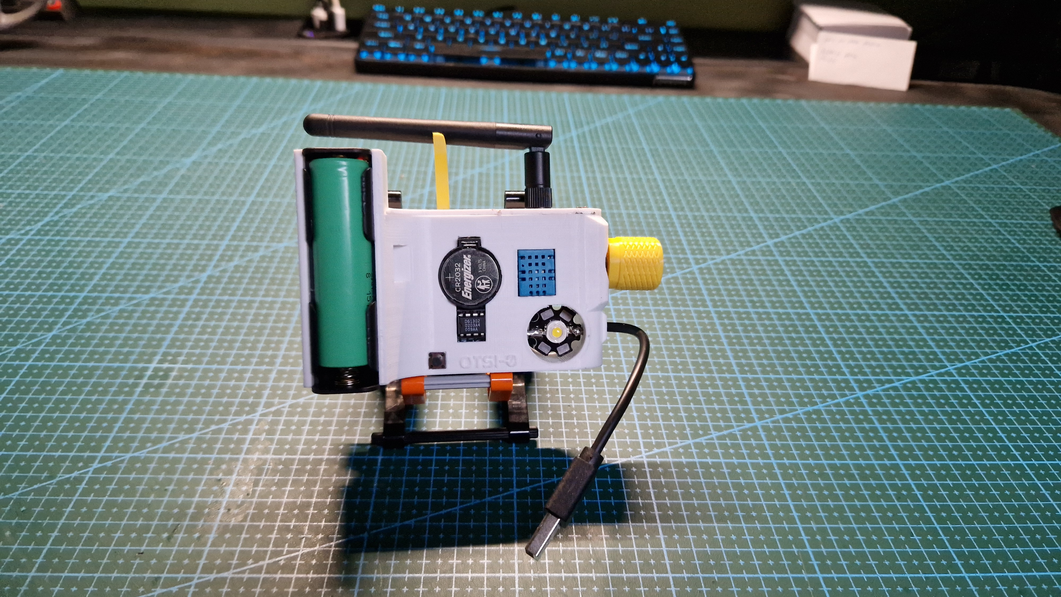
photos/20240127_143712.jpg
