A-N-Ulab/OTSI-cyberpet/photos/20240127_143720.jpg

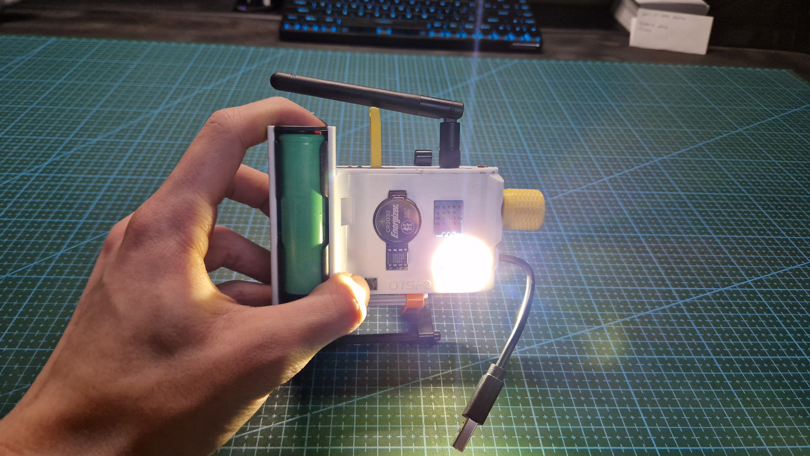
photos/20240127_143720.jpg
