A-N-Ulab/OTSI-cyberpet/photos/20240205_104920.jpg

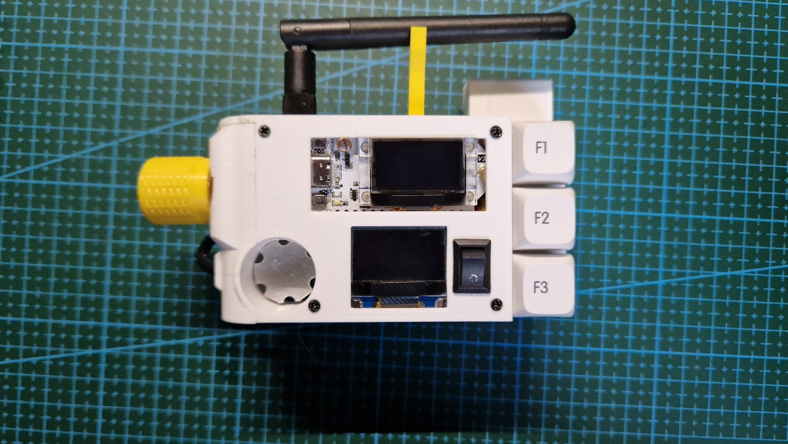
photos/20240205_104920.jpg
