A-N-Ulab/OTSI-cyberpet/photos/20240205_104932.jpg

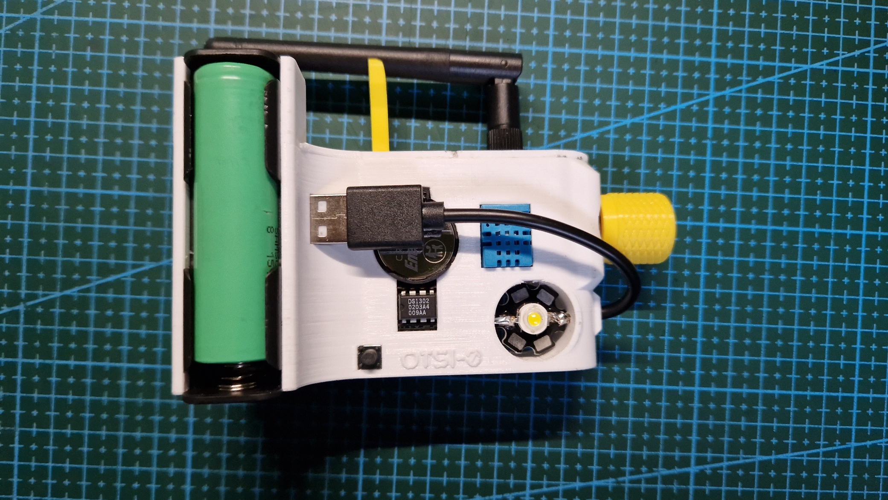
photos/20240205_104932.jpg
