A-N-Ulab/OTSI-cyberpet/photos/20240205_110011.jpg

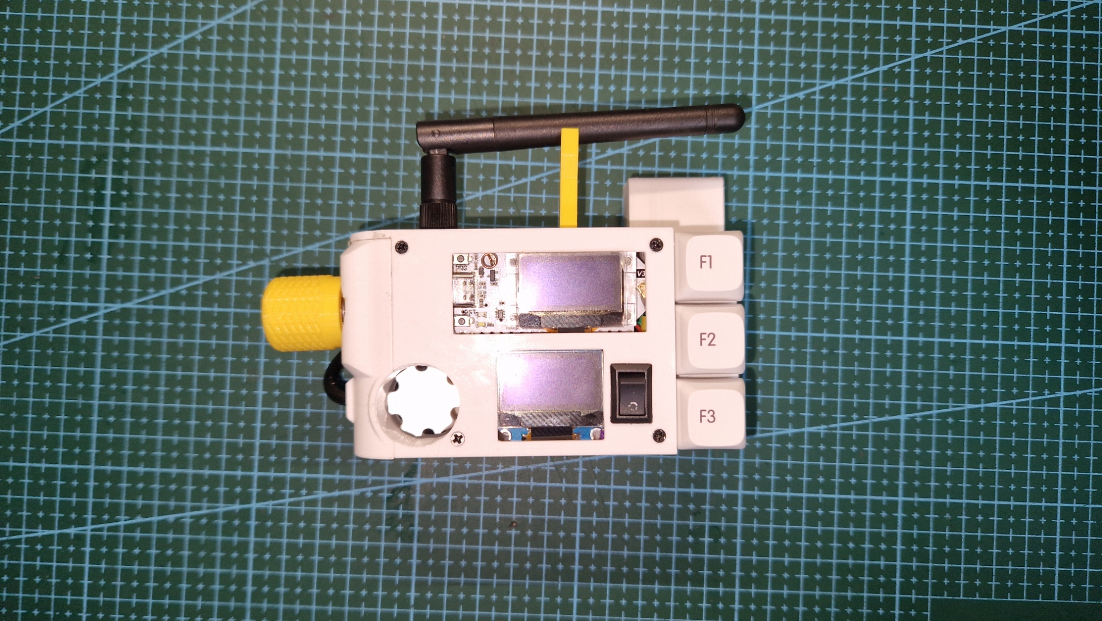
photos/20240205_110011.jpg
