A-N-Ulab/OTSI-cyberpet/photos/received_282160351365564.webp

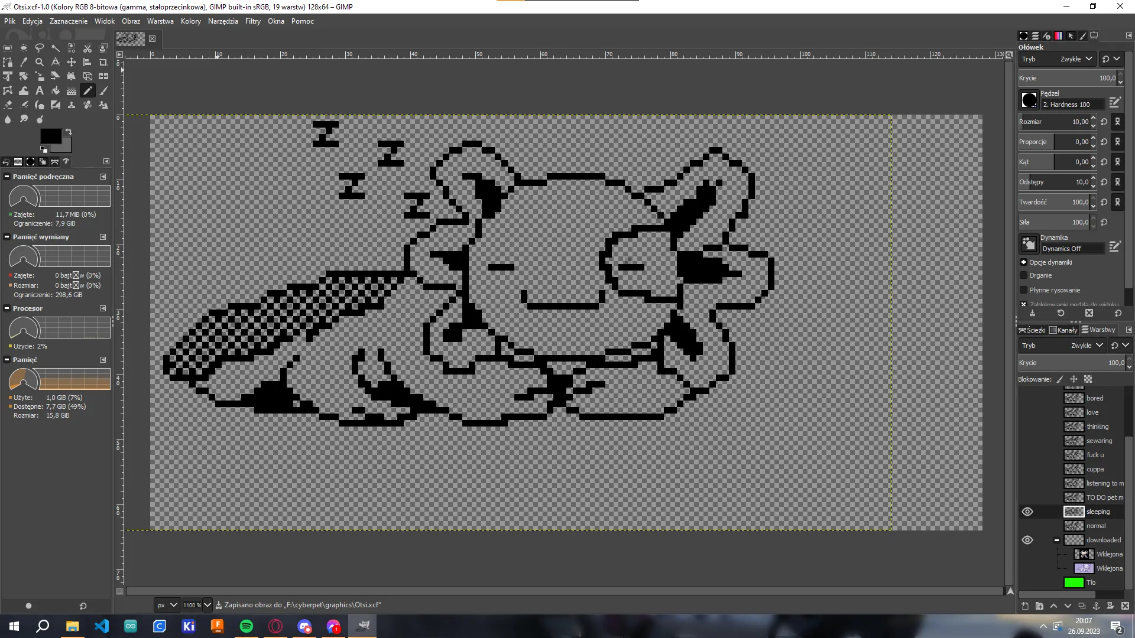
photos/received_282160351365564.webp
