A-N-Ulab/OTSI-cyberpet/photos/received_387716773831611.jpeg

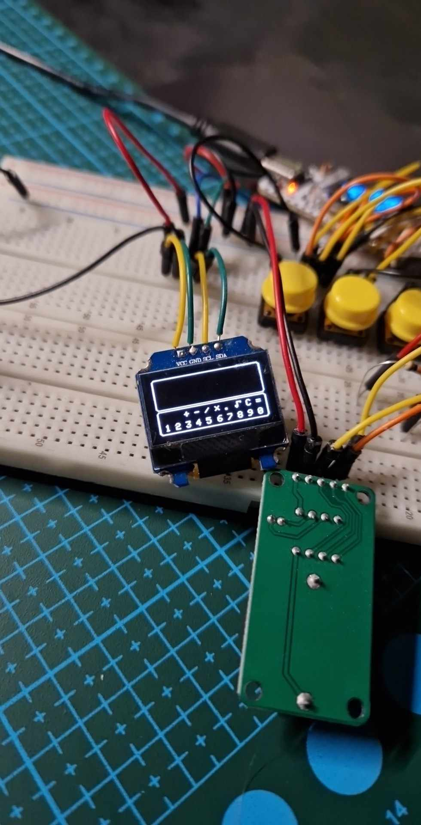
photos/received_387716773831611.jpeg
