A-N-Ulab/OTSI-cyberpet/photos/received_673554004835125.webp

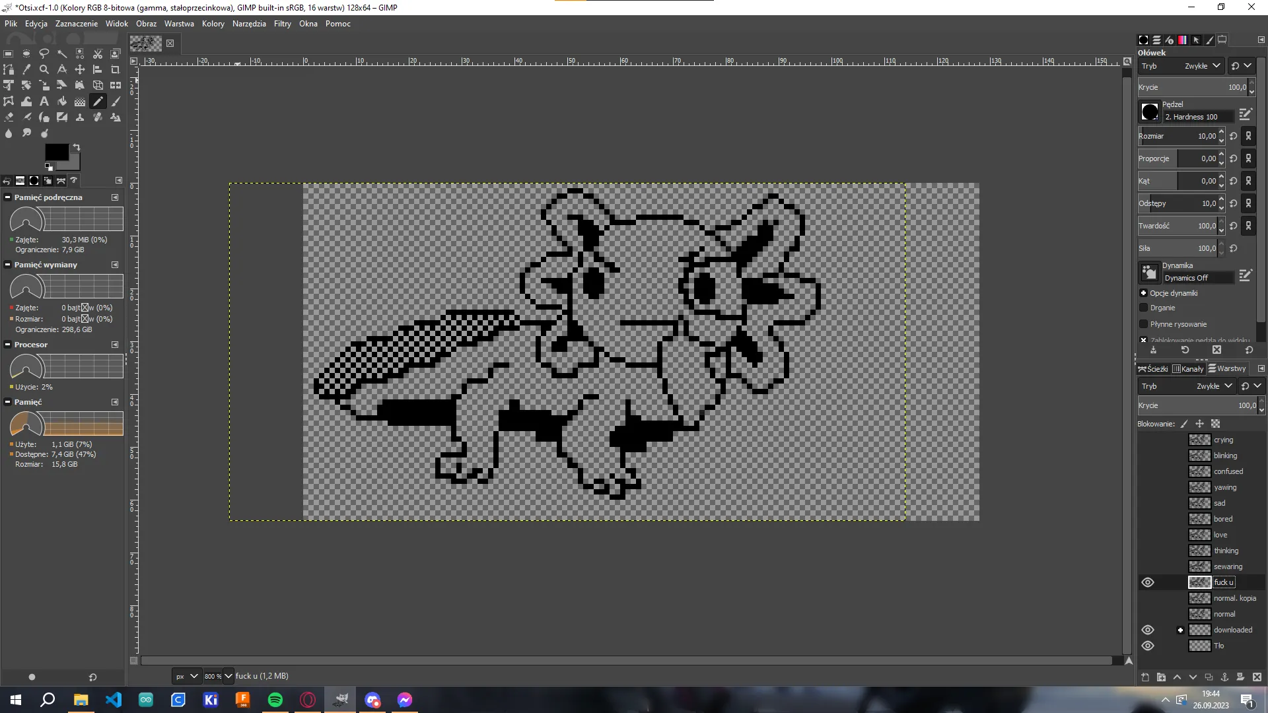
photos/received_673554004835125.webp
