A-N-Ulab/OTSI-cyberpet/photos/received_1347835669166146.webp

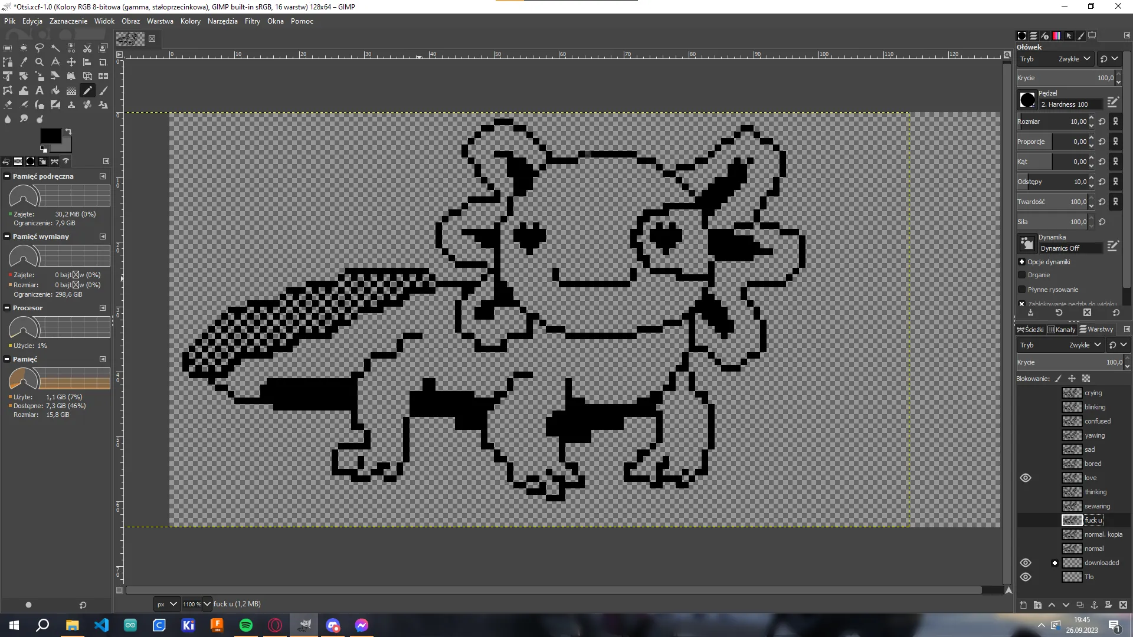
photos/received_1347835669166146.webp
