A-N-Ulab/OTSI-cyberpet/photos/Screenshot_20231015_171014_Instagram.jpg

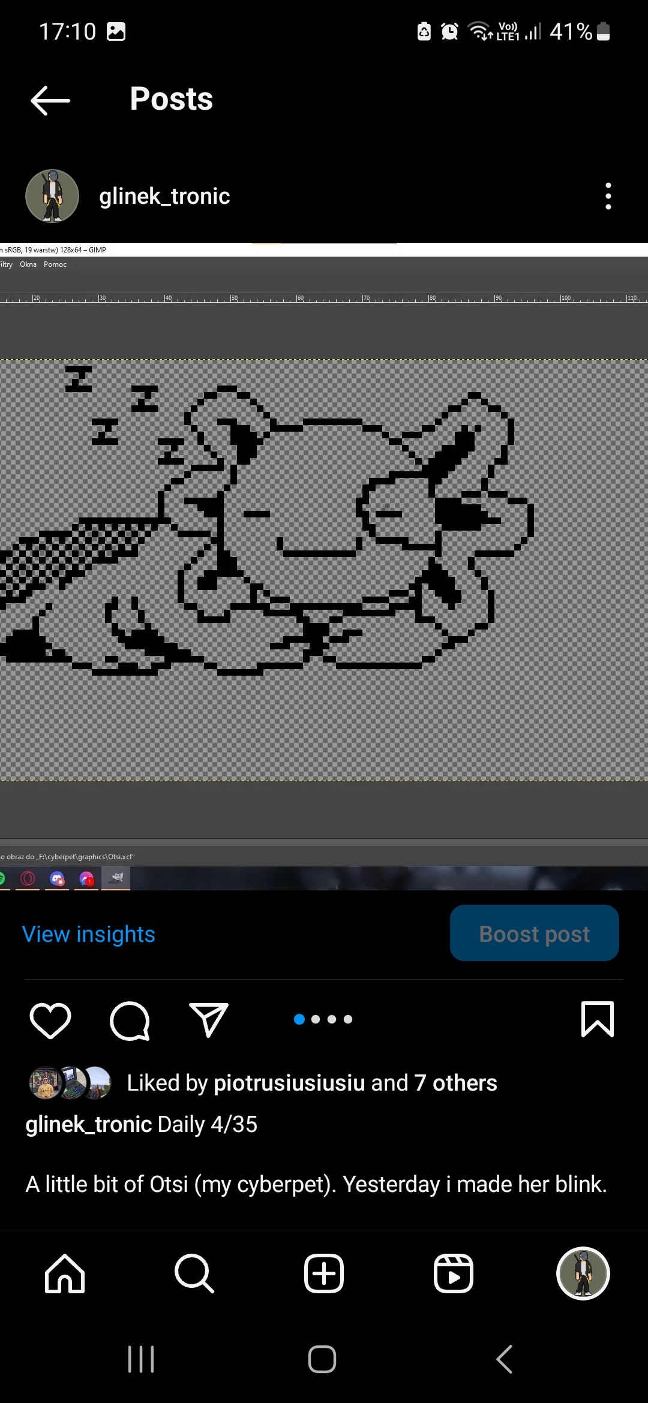
photos/Screenshot_20231015_171014_Instagram.jpg
