A-N-Ulab/OTSI-cyberpet/instructions/otsi schematic/otsi schematic.kicad_sch

## KiCad design instructions/otsi schematic/otsi schematic.kicad_sch (2025-07-11)

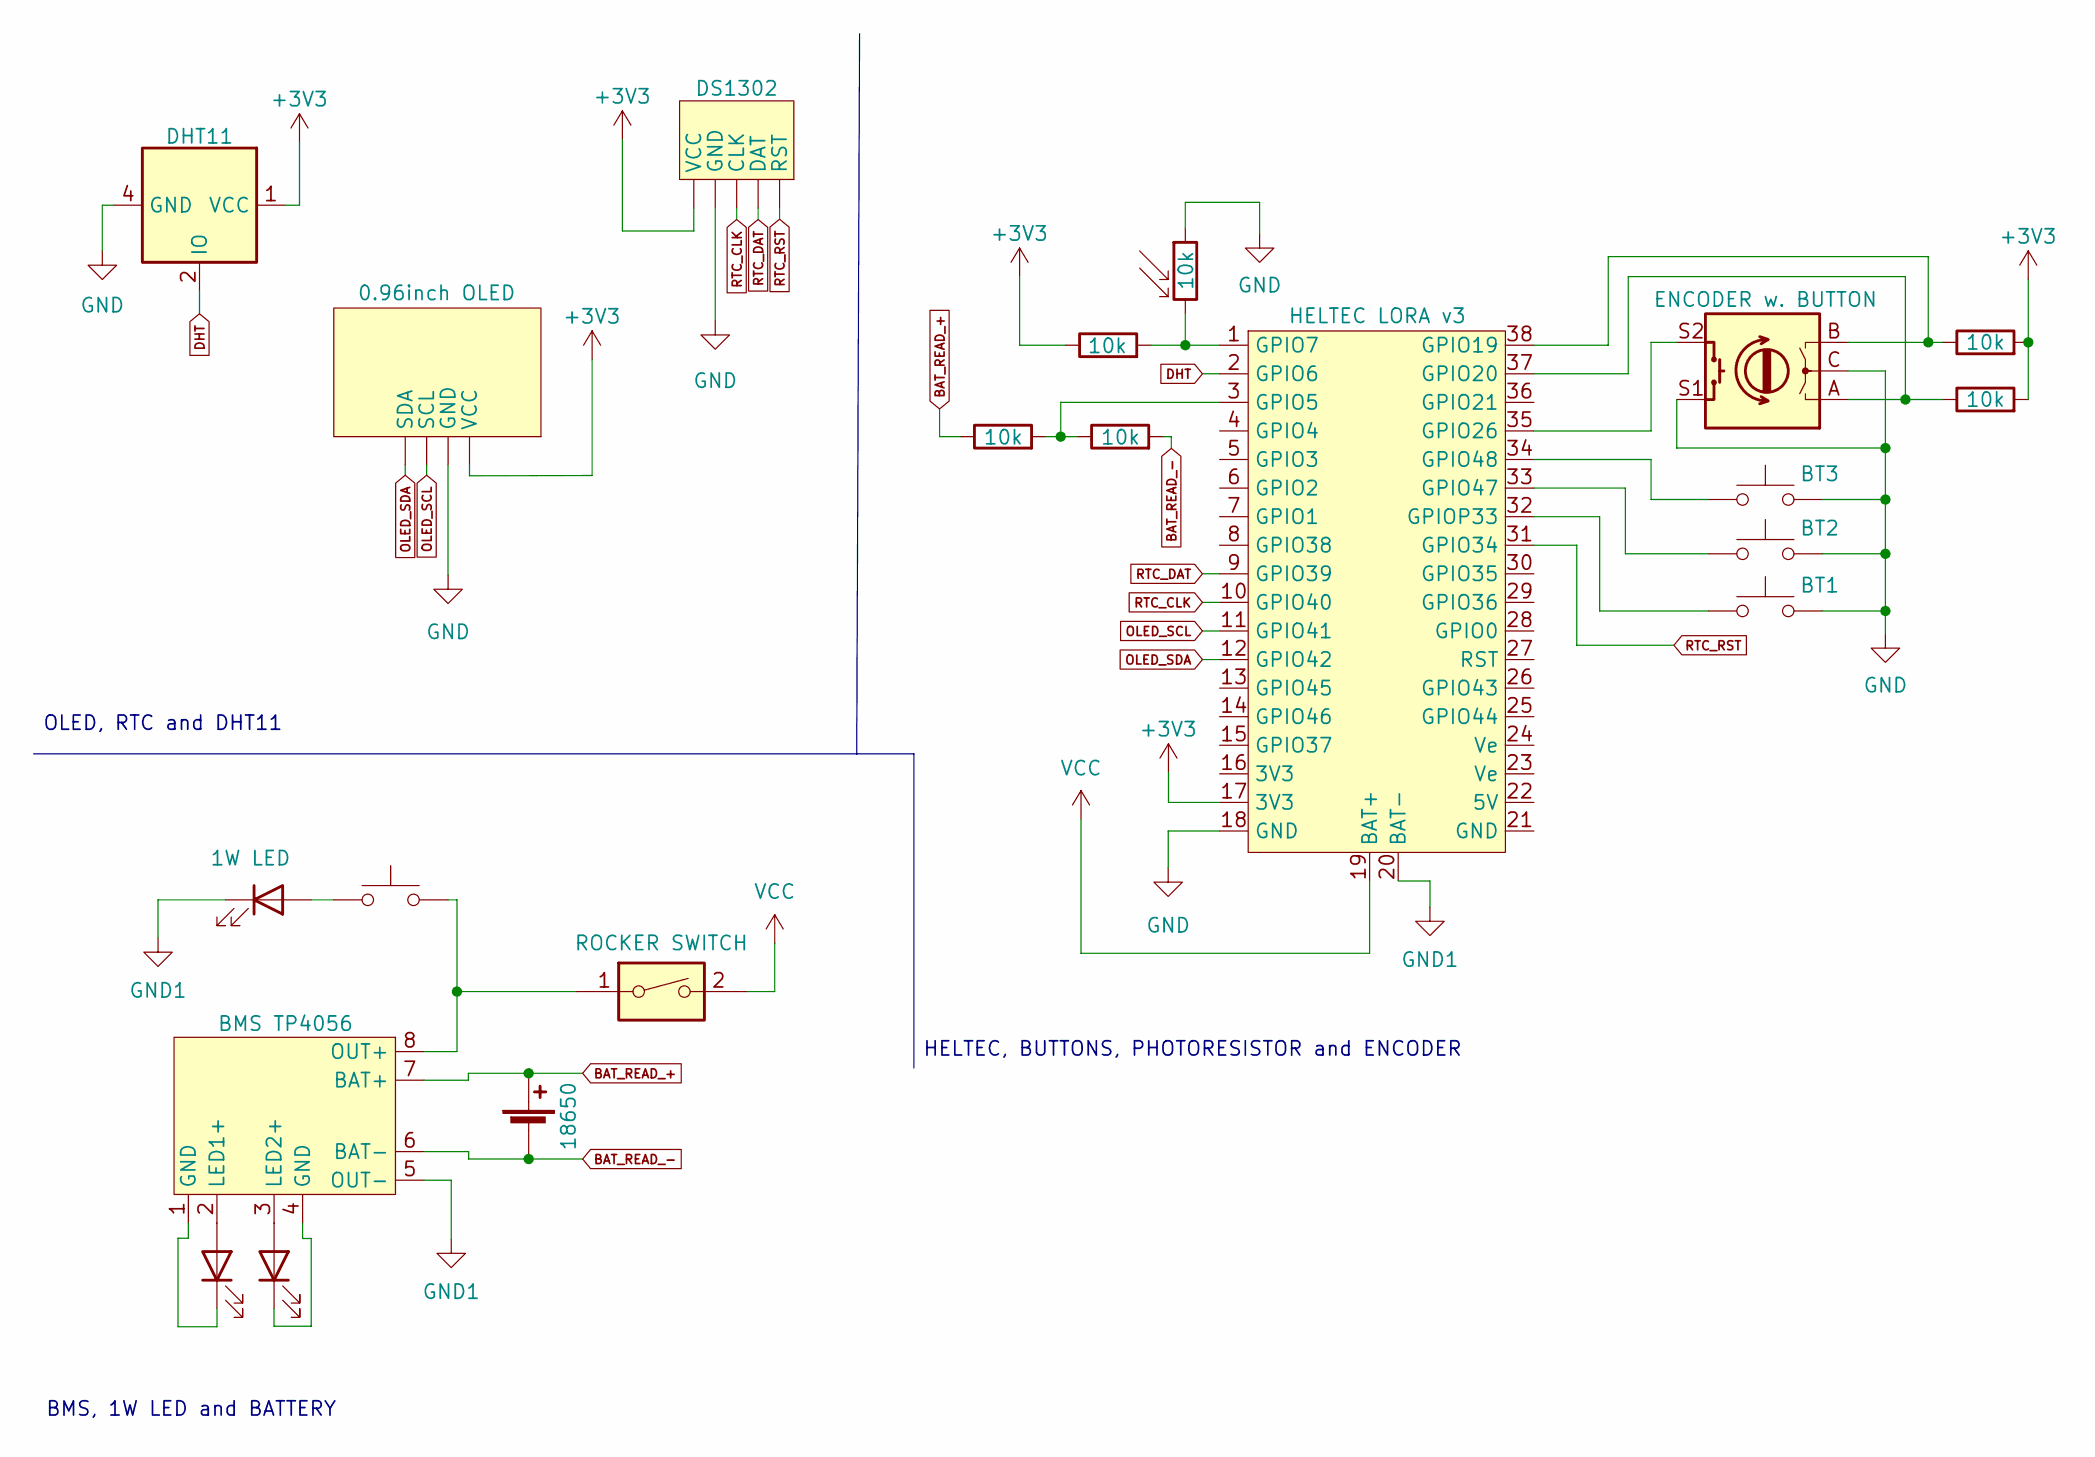
[picture p162: schematic otsi schematic.kicad_sch]

Parts:
BT1: 18650
BT2, BT3: SW_Push
D1, D3: LED
D2: 1W LED
R1, R2, R3, R4, R5, R6: 10k
SW1: SW_Push
SW2: ROCKER SWITCH
SW3: ENCODER w. BUTTON
U1: DHT11; Aosong_DHT11_5.5x12.0_P2.54mm
U2: BMS TP4056
U3: 0.96inch OLED
U4: DS1302
U5: HELTEC LORA v3

Connections:
+3V3: R2.1, R5.2, R6.2, U1.1 (VCC), U3., U4., U5.17 (3V3)
BAT_READ_+: BT1.1, R1.1, U2.7 (BAT+)
BAT_READ_-: BT1.2, R3.2, U2.6 (BAT-)
DHT: U1.2 (IO), U5.2 (GPIO6)
GND: BT1.2, BT2.2, BT3.2, R4.1, SW3.C, SW3.S1, U1.4 (GND), U3., U4., U5.18 (GND)
GND1: D2.1 (K), U2.5 (OUT-), U5.20 (BAT-)
unnamed: BT1.1, U5.32 (GPIOP33)
unnamed: BT2.1, U5.33 (GPIO47)
unnamed: BT3.1, U5.34 (GPIO48)
unnamed: D1.1 (K), U2.1 (GND)
unnamed: D1.2 (A), U2.2 (LED1+)
unnamed: D2.2 (A), SW1.1
unnamed: D3.1 (K), U2.4 (GND)
unnamed: D3.2 (A), U2.3 (LED2+)
unnamed: R1.2, R3.1, U5.3 (GPIO5)
unnamed: R2.2, R4.2, U5.1 (GPIO7)
unnamed: R5.1, SW3.B, U5.38 (GPIO19)
unnamed: R6.1, SW3.A, U5.37 (GPIO20)
unnamed: SW1.2, SW2.1, U2.8 (OUT+)
unnamed: SW3.S2, U5.35 (GPIO26)
OLED_SCL: U3., U5.11 (GPIO41)
OLED_SDA: U3., U5.12 (GPIO42)
RTC_CLK: U4., U5.10 (GPIO40)
RTC_DAT: U4., U5.9 (GPIO39)
RTC_RST: U4., U5.31 (GPIO34)
VCC: SW2.2, U5.19 (BAT+)

Notes on the sheet:
BMS, 1W LED and BATTERY
OLED, RTC and DHT11
HELTEC, BUTTONS, PHOTORESISTOR and ENCODER
