A-N-Ulab/OTSI-cyberpet/code/code22-encoder_password/images.h

#ifndef IMAGES_H
#define IMAGES_H

const static char otsi_crying[] = {
  0x00, 0x00, 0x00, 0x00, 0x00, 0x00, 0x00, 0x00, 0x00, 0x00, 0x00, 0x00, 0x00, 0x00, 0x00, 0x00, 
	0x00, 0x00, 0x00, 0x00, 0x00, 0x00, 0x38, 0x00, 0x00, 0x00, 0x00, 0x00, 0x00, 0x00, 0x00, 0x00, 
	0x00, 0x00, 0x00, 0x00, 0x00, 0x00, 0xc6, 0x00, 0x00, 0x00, 0x00, 0xc0, 0x00, 0x00, 0x00, 0x00, 
	0x00, 0x00, 0x00, 0x00, 0x00, 0x01, 0x01, 0x00, 0x00, 0x00, 0x01, 0x20, 0x00, 0x00, 0x00, 0x00, 
	0x00, 0x00, 0x00, 0x00, 0x00, 0x02, 0x00, 0x80, 0x00, 0x00, 0x06, 0x18, 0x00, 0x00, 0x00, 0x00, 
	0x00, 0x00, 0x00, 0x00, 0x00, 0x04, 0x00, 0x40, 0x00, 0x00, 0x08, 0x04, 0x00, 0x00, 0x00, 0x00, 
	0x00, 0x00, 0x00, 0x00, 0x00, 0x04, 0x38, 0x21, 0xff, 0x00, 0x10, 0x02, 0x00, 0x00, 0x00, 0x00, 
	0x00, 0x00, 0x00, 0x00, 0x00, 0x02, 0x0e, 0x3e, 0x00, 0xe0, 0x61, 0x42, 0x00, 0x00, 0x00, 0x00, 
	0x00, 0x00, 0x00, 0x00, 0x00, 0x01, 0x0f, 0x40, 0x00, 0x13, 0x83, 0x82, 0x00, 0x00, 0x00, 0x00, 
	0x00, 0x00, 0x00, 0x00, 0x00, 0x01, 0x0f, 0x80, 0x00, 0x0c, 0x03, 0x82, 0x00, 0x00, 0x00, 0x00, 
	0x00, 0x00, 0x00, 0x00, 0x00, 0x00, 0x87, 0x00, 0x00, 0x02, 0x0f, 0x84, 0x00, 0x00, 0x00, 0x00, 
	0x00, 0x00, 0x00, 0x00, 0x00, 0x00, 0x47, 0x00, 0x00, 0x01, 0x1f, 0x04, 0x00, 0x00, 0x00, 0x00, 
	0x00, 0x00, 0x00, 0x00, 0x00, 0x00, 0x26, 0x00, 0x00, 0x00, 0xbe, 0x0c, 0x00, 0x00, 0x00, 0x00, 
	0x00, 0x00, 0x00, 0x00, 0x00, 0x03, 0xe8, 0x00, 0x00, 0x00, 0x7c, 0x10, 0x00, 0x00, 0x00, 0x00, 
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
	0x01, 0xff, 0xfe, 0x00, 0x01, 0xff, 0xfe, 0x00, 0x01, 0xff, 0xfe, 0x00, 0x01, 0xff, 0xfe, 0x00, 
	0x01, 0xc7, 0x8e, 0x00, 0x01, 0xc7, 0x8e, 0x00, 0x01, 0xc7, 0x8e, 0x00, 0x00, 0x00, 0x00, 0x00
 };


#endif
