A-N-Ulab/OTSI-cyberpet/code/code01-display_test/HT_SSD1306Wire.h

#ifndef SSD1306Wire_h
#define SSD1306Wire_h

#include "HT_Display.h"
#include <Wire.h>


class SSD1306Wire : public ScreenDisplay {
  private:
      uint8_t             _address;
      int                 _sda;
      int                 _scl;
      uint32_t             _freq;
      bool                _doI2cAutoInit = false;

  public:
    SSD1306Wire(uint8_t _address, uint32_t _freq, int sda,int scl, DISPLAY_GEOMETRY g = GEOMETRY_128_64,int8_t _rst=-1) {
      setGeometry(g);
      setRst(_rst);
      this->_address = _address;
      this->_freq = _freq;
      this->_sda = sda;
      this->_scl = scl;
      this->displayType = OLED;
    }

    bool connect() {
      Wire.begin(_sda,_scl,_freq);
      return true;
    }

	void display(void) {
		initI2cIfNeccesary();
		if(rotate_angle==ANGLE_0_DEGREE||rotate_angle==ANGLE_180_DEGREE)
		{
		#ifdef DISPLAY_DOUBLE_BUFFER
			uint8_t minBoundY = UINT8_MAX;
			uint8_t maxBoundY = 0;

			uint8_t minBoundX = UINT8_MAX;
			uint8_t maxBoundX = 0;
			uint8_t x, y;

			// Calculate the Y bounding box of changes
			// and copy buffer[pos] to buffer_back[pos];
			for (y = 0; y < (this->height() / 8); y++)
			{
				for (x = 0; x < this->width(); x++)
				{
					uint16_t pos = x + y * this->width();
					if (buffer[pos] != buffer_back[pos]) 
					{
						minBoundY = _min(minBoundY, y);
						maxBoundY = _max(maxBoundY, y);
						minBoundX = _min(minBoundX, x);
						maxBoundX = _max(maxBoundX, x);
					}
					buffer_back[pos] = buffer[pos];
				}
				//yield();
			}

			// If the minBoundY wasn't updated
			// we can savely assume that buffer_back[pos] == buffer[pos]
			// holdes true for all values of pos

			if (minBoundY == UINT8_MAX) return;

			sendCommand(COLUMNADDR);
#ifdef Wireless_Stick_V3
      sendCommand( minBoundX+32);
      sendCommand( maxBoundX+32);
#else
      sendCommand( minBoundX);
      sendCommand( maxBoundX);
#endif
			sendCommand(PAGEADDR);
			sendCommand(minBoundY);
			sendCommand(maxBoundY);

			byte k = 0;
			for (y = minBoundY; y <= maxBoundY; y++)
			{
				for (x = minBoundX; x <= maxBoundX; x++)
				{
					if (k == 0)
					{
						Wire.beginTransmission(_address);
						Wire.write(0x40);
					}

					Wire.write(buffer[x + y * this->width()]);
					k++;
					if (k == 16)
					{
						Wire.endTransmission();
						k = 0;
					}
				}
				//yield();
			}

			if (k != 0) {
				Wire.endTransmission();
			}
		#else

			sendCommand(COLUMNADDR);
			sendCommand(0);
			sendCommand((this->width() - 1));

			sendCommand(PAGEADDR);
			sendCommand(0x0);

			if (geometry == GEOMETRY_128_64)
			{
				sendCommand(0x7);
			}
			else if (geometry == GEOMETRY_128_32)
			{
				sendCommand(0x3);
			}

			for (uint16_t i=0; i < displayBufferSize; i++)
			{
				Wire.beginTransmission(this->_address);
				Wire.write(0x40);
				for (uint8_t x = 0; x < 16; x++)
				{
					Wire.write(buffer[i]);
					i++;
				}
				i--;
				Wire.endTransmission();
			}
		#endif
		}
		else
		{
			uint8_t buffer_rotate[displayBufferSize];
			memset(buffer_rotate,0,displayBufferSize);
			uint8_t temp;
			for(uint16_t i=0;i<this->width();i++)
			{
				for(uint16_t j=0;j<this->height();j++)
				{
					temp = buffer[(j>>3)*this->width()+i]>>(j&7)&0x01;
					buffer_rotate[(i>>3)*this->height()+j]|=(temp<<(i&7));
				}
			}
		#ifdef DISPLAY_DOUBLE_BUFFER
			uint8_t minBoundY = UINT8_MAX;
			uint8_t maxBoundY = 0;
			 
			uint8_t minBoundX = UINT8_MAX;
			uint8_t maxBoundX = 0;
			uint8_t x, y;
			 
			// Calculate the Y bounding box of changes
			// and copy buffer[pos] to buffer_back[pos];
			for (y = 0; y < (this->width() / 8); y++)
			{
				for (x = 0; x < this->height(); x++)
				{
					uint16_t pos = x + y * this->height();
					if (buffer_rotate[pos] != buffer_back[pos])
					{
						minBoundY = _min(minBoundY, y);
						maxBoundY = _max(maxBoundY, y);
						minBoundX = _min(minBoundX, x);
						maxBoundX = _max(maxBoundX, x);
					}
					buffer_back[pos] = buffer_rotate[pos];
				}
				//yield();
			}
			if (minBoundY == UINT8_MAX) return;

			sendCommand(COLUMNADDR);
#ifdef Wireless_Stick_V3
      sendCommand( minBoundX+32);
      sendCommand( maxBoundX+32);
#else
      sendCommand( minBoundX);
      sendCommand( maxBoundX);
#endif
			sendCommand(PAGEADDR);
			sendCommand(minBoundY);
			sendCommand(maxBoundY);

			byte k = 0;
			for (y = minBoundY; y <= maxBoundY; y++)
			{
				for (x = minBoundX; x <= maxBoundX; x++)
				{
					if (k == 0)
					{
						Wire.beginTransmission(_address);
						Wire.write(0x40);
					}

					Wire.write(buffer_rotate[x + y * this->height()]);
					k++;
					if (k == 16)
					{
						Wire.endTransmission();
						k = 0;
					}
				}
				//yield();
			}

			if (k != 0) {
				Wire.endTransmission();
			}
		#else
			sendCommand(COLUMNADDR);
			sendCommand(0);
			sendCommand((this->height() - 1));

			sendCommand(PAGEADDR);
			sendCommand(0x0);

			if (geometry == GEOMETRY_128_64)
			{
				sendCommand(0x7);
			}
			else if (geometry == GEOMETRY_128_32)
			{
				sendCommand(0x3);
			}

			for (uint16_t i=0; i < displayBufferSize; i++)
			{
				Wire.beginTransmission(this->_address);
				Wire.write(0x40);
				for (uint8_t x = 0; x < 16; x++)
				{
					Wire.write(buffer_rotate[i]);
					i++;
				}
				i--;
				Wire.endTransmission();
			}
		#endif
		}
	}

    void setI2cAutoInit(bool doI2cAutoInit) {
      _doI2cAutoInit = doI2cAutoInit;
    }

	void stop(){
		end();
		Wire.end();
	}
  private:
	int getBufferOffset(void) {
		return 0;
	}
    inline void sendCommand(uint8_t command) __attribute__((always_inline)){
      initI2cIfNeccesary();
      Wire.beginTransmission(_address);
      Wire.write(0x80);
      Wire.write(command);
      Wire.endTransmission();
    }

    void initI2cIfNeccesary() {
      if (_doI2cAutoInit) {
      	Wire.begin(_sda,_scl,_freq);
      }
    }

void sendInitCommands(void) 
	{
		if (geometry == GEOMETRY_RAWMODE)
			return;
		sendCommand(DISPLAYOFF);
		sendCommand(SETDISPLAYCLOCKDIV);
		sendCommand(0xF0); // Increase speed of the display max ~96Hz
		sendCommand(SETMULTIPLEX);
		sendCommand(this->height() - 1);
		sendCommand(SETDISPLAYOFFSET);
		sendCommand(0x00);
		sendCommand(SETSTARTLINE);
		sendCommand(CHARGEPUMP);
		sendCommand(0x14);
		sendCommand(MEMORYMODE);
		sendCommand(0x00);
		sendCommand(SEGREMAP|0x01);
		sendCommand(COMSCANDEC);
		sendCommand(SETCOMPINS);
sendCommand(0x12);

//		if (geometry == GEOMETRY_128_64) {
//		sendCommand(0x12);
//		} else if (geometry == GEOMETRY_128_32) {
//		sendCommand(0x02);
//		}

		sendCommand(SETCONTRAST);
sendCommand(0xCF);
/*
		if (geometry == GEOMETRY_128_64) {
		sendCommand(0xCF);
		} else if (geometry == GEOMETRY_128_32) {
		sendCommand(0x8F);
		}
*/
		sendCommand(SETPRECHARGE);
		sendCommand(0xF1);
		sendCommand(SETVCOMDETECT); //0xDB, (additionally needed to lower the contrast)
		sendCommand(0x40);			//0x40 default, to lower the contrast, put 0
		sendCommand(DISPLAYALLON_RESUME);
		sendCommand(NORMALDISPLAY);
		sendCommand(0x2e);			  // stop scroll
		sendCommand(DISPLAYON);
	}
	
	void sendScreenRotateCommand(){
		switch(this->rotate_angle)
		{
			case ANGLE_0_DEGREE:
				sendCommand(SEGREMAP|0x01); // Set Segment Re-map	//a1 mirror
				sendCommand(0xc8); // Set Common scan direction
				break;
			case ANGLE_90_DEGREE:
				sendCommand(SEGREMAP); // Set Segment Re-map   //a1 mirror
				sendCommand(0xc8); // Set Common scan direction
				break;
			case ANGLE_180_DEGREE:
				sendCommand(SEGREMAP); // Set Segment Re-map   //a1 mirror
				sendCommand(0xc0); // Set Common scan direction
				break;
			case ANGLE_270_DEGREE:
				sendCommand(SEGREMAP|0x01); // Set Segment Re-map	//a1 mirror
				sendCommand(0xc0); // Set Common scan direction
				break;
			default:
				break;
		}
	}

};

#endif
