A-N-Ulab/OTSI-cyberpet/photos/20240124_092052.jpg

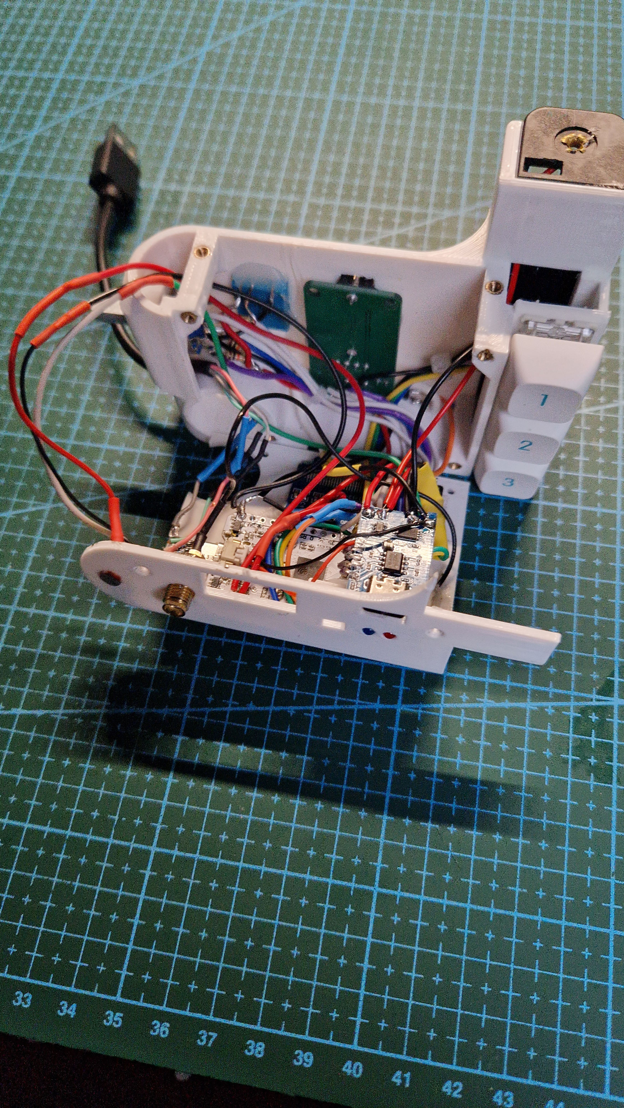
photos/20240124_092052.jpg
