A-N-Ulab/OTSI-cyberpet/photos/20240127_142557.jpg

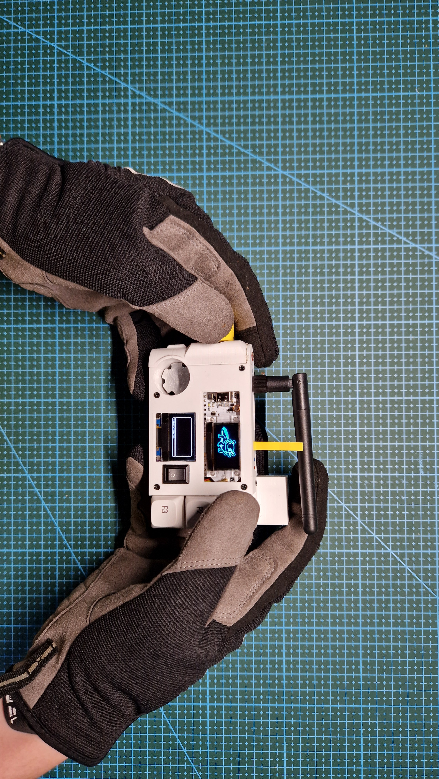
photos/20240127_142557.jpg
